open-pe/smart-shunt-fw/doc/thermal emf.md

i did some measurements to show the effects of thermoelectric force.

ADC: INA228, 40mV range
Resistor: Riedon RSN 50A 50mV (1mΩ)
Connection: blank copper wire soldered on SMD pads, blank copper wire on shunt resistor (see pictures below)




C
