open-pe/smart-shunt-fw/doc/ads131.md

internal Vref=1.2V

to measure DC voltage over FSR, connect AIN- to Vref.
Then AIN+ can have a voltage of 2.4V relative to GND.
Voltage divider: 3/100kΩ
=> measure voltages up to 82.4 V

Resistors:

TNPU06033K01BZEN00 (3.01k, 5ppm/K)
TNPU0603100KBZEN00 (100k, 5ppm/K)

2ppm/K:
susumu RG2012L-333-L-T05 (33k)
vishay P2TC0603D1003LNTA (100k)

0.2ppm/K:
Y201575K0000T9L (75k)
Y1633125K000T9R (125k, 2512)
Y4027125K000T9R (125k, 2512)
Y1627100K000T9R (100k, 2512)
Y1628150K000T9R (150k, 2512)
Y162750K0000T9R (50k, 2512)
