open-pe/smart-shunt-fw/doc/chopper.md

# voltage
- some DMM (the DMM6500) have the ability to measure voltage ratio
- multiplexers
  - TMUX8612RUMR: 100V multiplexer (20Ω)
  - TMUX8212RUMR (7Ω)
