open-pe/smart-shunt-fw/doc/Data Logging.md

https://github.com/PhilippCo/meas_rpi

https://github.com/PhilippCo/testgear

mreps github multistrumentalist

https://www.eevblog.com/forum/metrology/raspberry-pi23-logging-platform-for-voltnuts/
