open-pe/smart-shunt-fw/doc/Shunt Resistors.md

Considerations choosing the shunt / burden / current sense resistor:

* Current sense amplifier voltage range. INA228 has 2 ranges: ±163.84 mV and ±40.96 mV

## Riedon RSN series 0.1% ±15ppm/°C

* +-0.02% temp range (15-80°C)
* 50mV or 100mV output (for ina228 the 50mV is a good choice)
* RSN-20 (13.3A cont.), 2.5 or 5 mOhm
* RSN-50 (33.3 A cont.), 1 or 2 mOhm

## RESI RTC/RTB 0.1% ±20ppm/°C

* RTCS0100B050Z00 0.5mΩ ±0.1% ±20ppm/°C
* RTBS0200B075Z00 0.375mΩ ±0.1% ±20ppm/°C

## Riedon RS series 0.25%

## Murata DMS series 0.25% 15ppm (discontinued)

## CN XIQI DC Shunt Resistor 0.5%
* datasheet: "The ambient temperature changes by 10 °C, and the output signal of the shunt does not
  exceed 50% error of the accuracy"

* no info about temp coefficient

# Very low temp coefficient

* VPG Foil Resistors
    * PSBWR0010B
    * PSBXR0050B 5mOhm 0.1% ±5ppm/°C

# Smart Current Sensor

* SSA-100 (0.1%)
* +- 0.1 % upper temp range (10-50°C)
* CMRR: -100dB @ DC
* SNR: VIN = 100 mVPP, fIN = 1 kHz, BW = 10 kHz 80dB min 84dB typica

# Calibration 
https://www.fluke.com/de-de/produkt/kalibratoren/elektrische-kalibrierung/elektrische-normale/a40b
https://www.goldeno.com/pictures/CH48T4HK.pdf

https://www.distrelec.de/en/power-resistor-100mohm-250w-isabellenhuette-rug-r100-tk1/p/16057585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
https://www.distrelec.de/en/power-resistor-10mohm-250w-isabellenhuette-rug-r010-tk1/p/16057583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
