open-pe/smart-shunt-fw/src/relay_mux.h

#pragma once

#include <Arduino.h>
#include <atomic>
#include "util.h"

/*
 * Coto 3502 relay mux, revision A -- two-channel differential input selector.
 *
 * Board: ~/dev/ee/hw/dmm-mux-TMUX862/relay-mux (DESIGN.md dated 2026-08-21) is the
 * authority for everything asserted here. Two Coto 3502-05-511 DPST Form-A reed
 * relays select input A or input B onto one isolated output pair; on this bench the
 * output goes through the ads1262-divider board into one ADS1262 input pair.
 *
 * WHAT THE HARDWARE DOES FOR US, and therefore what this driver must not duplicate:
 *
 *   NREQ_A  = not REQ_A
 *   NREQ_B  = not REQ_B
 *   VALID_A = ARM and REQ_A and NREQ_B
 *   VALID_B = ARM and REQ_B and NREQ_A
 *
 * One-hot is decoded in 74HCT11/74HCT14 logic, so "both requests high" energises
 * NEITHER coil: no firmware bug can COMMAND two coils at once. That is a statement
 * about coil drive and nothing more -- it does not prove the mechanical contacts
 * cannot overlap, which depends on release and operate times DESIGN.md still lists
 * as qualification items. A TPS3840 supervisor and a common-return MOSFET (Q3,
 * gated by ARM) cut coil current independently of either driver. Every J4 logic
 * input carries a 10k series resistor into a 100k pull-down, so all three lines LOW
 * -- which is also what a floating, unprogrammed or reset MCU presents -- means both
 * coils released.
 *
 * So there is no state to restore at boot, and a RESET releases both coils. A HANG
 * does not: a wedged task leaves the output latches driving whatever they last
 * drove, ARM included. DESIGN.md accepts static ARM for revision A and leaves a
 * watchdog-qualified ARM as an open system-level option; this firmware does not
 * provide one.
 *
 * WHAT THE HARDWARE DOES NOT DO, and is therefore this driver's whole job: the
 * documented switching sequence, and the waiting.
 *
 *   1. Deassert ARM.
 *   2. Set REQ_A = REQ_B = 0.
 *   3. Wait for contact release and dead time.
 *   4. Preload exactly one request.
 *   5. Assert ARM.
 *   6. Wait for relay AND measurement settling before accepting data.
 *
 * Steps 3 and 6 are the ones that cost real time, and skipping them does not fail
 * loudly -- it publishes a plausible voltage measured through a contact that was
 * still bouncing, or through the wrong input entirely.
 *
 * 3.3 V DRIVE: ARGUED, NOT GUARANTEED. J4's contract is that it receives at least
 * VOH 3.10 V. The logic inputs are ~110k to ground and draw ~30 uA, so an ESP32 pin
 * loaded this lightly sits at essentially VDD; 3.3 V through the 10k/100k divider
 * puts 3.0 V on the HCT input against a 2.0 V VIH, and 3.0 V on Q3's gate against
 * the PMV20XNEAR's 2.5 V specification. The arithmetic holds, but "VDD at 30 uA" is
 * a nominal-plus-light-load argument, not a datasheet VOH bound over supply,
 * temperature and cable drop -- and DESIGN.md leaves confirmation of all three
 * outputs open. MEASURE ARM/REQ_A/REQ_B at J4 before trusting a marginal harness.
 * The board still needs its own +5V_CTRL -- this drives logic only, never a coil.
 */
class RelayMux2 {
public:
    enum class Target : uint8_t { NONE = 0, CH_A = 1, CH_B = 2 };

    static const char *targetName(Target t) {
        switch (t) {
            case Target::CH_A: return "A";
            case Target::CH_B: return "B";
            default:           return "off";
        }
    }

    /* TIMING -- DELIBERATELY CONSERVATIVE, AND NOT YET QUALIFIED.
     *
     * DESIGN.md derives exactly one number for the delay-on network, 15.95 ms, and
     * it is the FASTEST corner (R = 0.80 M, C = 94.7 nF, VT+ = 1.2 V min). That
     * number exists to prove non-overlap -- it bounds how soon a coil can possibly
     * engage -- and it is the wrong end of the distribution for deciding when the
     * contact is definitely closed. The slow corner is not derived anywhere, and
     * DESIGN.md's open gates still say "Revision-A qualification must measure
     * contact release time" and "Logic timing and coil voltage do not prove contact
     * non-overlap". So these are engineering margins over an unmeasured quantity,
     * not datasheet limits.
     *
     * Nominal turn-on is around 1 M * 100 nF * ln(5/(5-VT+)) ~ 40 ms, and a slow
     * corner (R +20%, VT+ at the HCT14 maximum) lands near 65 ms. 250 ms is roughly
     * 4x that, plus reed operate time (sub-millisecond on the 3500 series), plus
     * bounce, plus the divider's own RC into the ADC.
     *
     * The cost of being generous is only rate: a full A/B alternation is about
     * 2 * (DEAD_TIME + SETTLE) plus the discarded conversions, so ~1 s. This is a
     * precision DC ratio front end, not a telemetry channel -- an averaging window
     * spans many alternations either way. TIGHTEN THESE ONLY AGAINST A SCOPE
     * TRACE of the actual contacts, which is what the board's qualification plan
     * asks for anyway; the console command below exists to make that measurement
     * possible without a rebuild. */
    /* DEAD TIME -- STILL A MARGIN OVER AN UNMEASURED QUANTITY (2026-09-03).
     *
     * Coto's 3500-series datasheet gives the 3502 a RELEASE TIME of 0.1 ms typical
     * (operate, including bounce, 0.75 ms). DO NOT SIZE THIS FROM THAT NUMBER --
     * an earlier revision of this comment did, and called 5 ms "50x the datasheet
     * release", which is not what the datasheet says about THIS board:
     *
     *   - The 0.1 ms is measured "At Nominal Coil Voltage, 30 Hz Square Wave" and
     *     the datasheet specifies no coil suppression at all. This board fits D3/D4,
     *     plain 1N4148W flyback diodes across the coils, which hold the coil current
     *     circulating with ~0.7 V of forcing and stretch the flux decay. DESIGN.md
     *     anticipates it in as many words: "change to a diode/Zener clamp only if
     *     the plain diode cannot meet dead-time requirements." The release time as
     *     built is an unmeasured MULTIPLE of 0.1 ms.
     *   - 0.1 ms is TYPICAL. Coto publishes no maximum.
     *
     * So DESIGN.md's open gate -- a scope-measured contact release time -- is not
     * closed, and this number is exactly what it was before the datasheet was read:
     * a margin.
     *
     * What makes 5 ms comfortable rather than brave is that the dead window is NOT
     * the primary non-overlap margin. On an A<->B alternation the INCOMING channel's
     * delay-on capacitor has been discharged for a whole dwell, so after ARM rises
     * that coil still needs 15.95 ms in its FASTEST corner (DESIGN.md, derived
     * expressly to bound how soon a coil can engage) before it can pull in. The dead
     * window is a SECOND, INDEPENDENT margin -- the one that survives a failed
     * delay-on network -- and 5 ms of it costs nothing at the current rate.
     *
     * NOTE FOR ANYONE TIGHTENING THIS FURTHER: the ADC cannot check your work.
     * A brief overlap dumps charge onto the divider output, which decays through
     * the divider's ~19.6 kOhm into 100 nF -- tau ~ 2 ms -- while the published
     * conversion ends 157 ms after ARM, some 80 tau later. A dead-time sweep read
     * by this ADC therefore returns "not detectable", never "not present". Use a
     * scope on the contacts, which is what DESIGN.md asked for in the first place. */
    static constexpr uint32_t DEAD_TIME_MS = 5;           ///< step 3: both coils released
    /// Lower clamp on the runtime dead time. Not a measurement -- see setDeadMs().
    static constexpr uint32_t DEAD_MIN_MS = 1;
    /* SETTLE -- 250 ms until 2026-09-03, when the reason for it was removed.
     *
     * 250 ms was a margin against the settling tail measured on this fixture, and
     * that tail was dielectric absorption in the shunt-adc board's X7R input caps.
     * With those replaced by C0G the tail is gone: the bias-vs-step slope at the
     * earliest reachable sample instant fell from -25.73 +- 0.86 to -0.24 +- 2.04
     * uV/V, consistent with zero (pwr-metering hw/shunt-adc finding F23).
     *
     * 30 ms is not an accuracy choice -- the published conversion still ends
     * 157 ms after ARM either way, because the converter free-runs and
     * DISCARD_SCANS = 2 lands the sample on the same conversion for ANY settle up
     * to one conversion period. It is a RATE choice: dead + settle <= 52.22 ms
     * keeps the dwell one whole conversion shorter. See the static_assert in
     * relay_mux_adc.h, which fails the build if that stops holding.
     *
     * IT WAS 45 ms FOR ONE DAY, AND THAT WAS TOO CLOSE TO THE EDGE. dead + settle
     * = 50 ms left 2.2 ms of margin against the 52.22 ms conversion, and the bench
     * spent most of its time on the wrong side of the boundary: round trips
     * quantised to 45 / 46 / 47 conversions (2.350 / 2.402 / 2.461 s) with 47 the
     * mode, against the 44 predicted. Cutting 15 ms moved the WHOLE distribution
     * down by one conversion per dwell, to 44 / 45 -- which a 15 ms change cannot
     * do to a ceil() of a 35-50 ms argument unless the argument is bigger than
     * dead + settle. It is: this timer is evaluated by realTimeTask, which also
     * ticks the mux and updates every sampler on each pass, so what gets rounded
     * up is dead + settle + LATENCY.
     *
     * 30 ms leaves 17.2 ms for that latency and stays 10 ms above SETTLE_FLOOR_MS.
     * Do not spend the margin. It does NOT buy determinism -- two thirds of round
     * trips still take the extra conversion, and that residual is unexplained (see
     * doc/relay-mux-front-end.md) -- but it is worth a whole conversion per dwell.
     *
     * The contact's own close is covered by the discards, not by this number: the
     * delay-on slow corner is 65 ms and the published conversion does not START
     * until 104.4 ms after ARM. */
    static constexpr uint32_t SETTLE_MS_DEFAULT = 30;    ///< step 6: contact closed and quiet

    /* Hard floor. No evidence from the ADC, however convincing, may publish a
     * sample sooner than this after ARM rises, because DESIGN.md's FASTEST
     * delay-on corner is 15.95 ms -- the contact CANNOT have closed before then.
     *
     * (An earlier comment said anything read before this is "the previous channel
     * holding still". That was wrong: steps 1-3 release BOTH coils during
     * DEAD_TIME_MS before ARM rises, so between ARM and contact close the ADC sees
     * an OPEN input, not the previous selection. The floor is still conservative,
     * but the misreading matters -- it is the same one that let the step guard in
     * relay_mux_adc.h treat "moved away from the other channel" as proof that this
     * channel had closed.)
     *
     * This is the one number in the settle path that is a real bound rather than
     * an estimate, and it is why the adaptive path cannot talk itself to zero. */
    static constexpr uint32_t SETTLE_FLOOR_MS = 20;

    /* Upper clamp on the runtime settle. Bounds both the auto-widen ratchet and a
     * fat-fingered console value; a settle beyond this is not a slow relay, it is
     * a fault worth reporting as one. */
    static constexpr uint32_t SETTLE_MAX_MS = 2000;

private:
    const uint8_t pinArm, pinReqA, pinReqB;

    enum class State : uint8_t {
        OFF,        ///< disarmed, no request, not switching
        DEAD_TIME,  ///< both requests cleared, waiting out contact release
        SETTLING,   ///< one request preloaded and ARM asserted, waiting for close
        SETTLED,    ///< contact believed closed and quiet; data may be trusted
    };

    State state = State::OFF;
    Target current = Target::NONE;   ///< what is (being) selected
    Target pending = Target::NONE;   ///< what select() asked for
    uint32_t tStateMs = 0;
    uint32_t tArmMs = 0;             ///< when ARM last rose; survives the SETTLED transition
    uint32_t armGen_ = 0;            ///< bumped once per ARM assertion (one per switch)
    uint32_t settleMs_ = SETTLE_MS_DEFAULT;
    uint32_t deadMs_ = DEAD_TIME_MS;
    uint32_t generation_ = 0;        ///< bumped once per entry into SETTLED
    bool begun = false;

    /// Written by any task via requestFromOtherTask(), consumed only in tick().
    std::atomic<uint8_t> inboxTarget{(uint8_t) Target::NONE};
    std::atomic<bool> inboxPending{false};

    void driveAll(bool arm, bool reqA, bool reqB) const {
        digitalWrite(pinArm, arm);
        digitalWrite(pinReqA, reqA);
        digitalWrite(pinReqB, reqB);
    }

public:
    RelayMux2(uint8_t pinArm, uint8_t pinReqA, uint8_t pinReqB)
        : pinArm(pinArm), pinReqA(pinReqA), pinReqB(pinReqB) {}

    /// False if any control pin is unassigned. 255 is settings.h's "not wired on
    /// this board" sentinel and pinMode(255) is an "Invalid IO" HAL error, not a
    /// no-op -- the same mistake that put three of them in every boot log when the
    /// INA228 mux backend was left enabled on a board with no mux.
    bool pinsConfigured() const {
        return pinArm != 255 && pinReqA != 255 && pinReqB != 255;
    }

    bool begin() {
        /* Idempotent. begin() is now called from setup() so the state machine runs
         * whether or not anything else on the board came up, and the ADC backend
         * calls it too; a second call must not reset a mux that is mid-sequence or
         * already settled on a channel. */
        if (begun) return true;
        if (!pinsConfigured()) {
            ESP_LOGE("relaymux", "control pins unset (ARM=%u REQ_A=%u REQ_B=%u); not starting",
                     pinArm, pinReqA, pinReqB);
            return false;
        }
        /* Level BEFORE direction. An output pin adopts its level at the moment it
         * becomes an output, so pinMode-then-write briefly drives whatever was in
         * the output latch -- and a stray high on ARM with a stale request latched
         * is a coil pulse. Writing first makes the first driven level a known LOW.
         * The board's own pull-downs cover the window before this runs. */
        digitalWrite(pinArm, LOW);
        digitalWrite(pinReqA, LOW);
        digitalWrite(pinReqB, LOW);
        pinMode(pinArm, OUTPUT);
        pinMode(pinReqA, OUTPUT);
        pinMode(pinReqB, OUTPUT);
        driveAll(LOW, LOW, LOW);
        state = State::OFF;
        current = Target::NONE;
        pending = Target::NONE;
        tStateMs = millis();
        begun = true;
        ESP_LOGI("relaymux", "ready: ARM=%u REQ_A=%u REQ_B=%u, dead %lums settle %lums",
                 pinArm, pinReqA, pinReqB,
                 (unsigned long) DEAD_TIME_MS, (unsigned long) settleMs_);
        return true;
    }

    /* CROSS-TASK COMMAND INBOX.
     *
     * select() mutates the state machine and MUST run only on the task that calls
     * tick() -- realTimeTask here. The console runs on appTask
     * (handleConsoleInput() is called from Telemetry::update()), so a console
     * command calling select() directly races tick().
     *
     * The race is not theoretical and not benign. select() writes `state` and
     * `tStateMs` as two separate stores; with `state` written first, tick() on the
     * other core can observe state == DEAD_TIME carrying the PREVIOUS tStateMs,
     * find the dead time already long expired, and assert ARM immediately. That
     * skips the entire contact-release wait -- the one thing this driver exists to
     * guarantee -- and re-energises the other coil while the first contact may
     * still be closed, briefly bridging two floating 0-80 V inputs.
     *
     * The board survives it: the 1 M/100 nF delay-on network cannot engage a coil
     * for at least ~16 ms (DESIGN.md's fastest corner), which is exactly why that
     * network exists. But that makes the hardware interlock load bearing in normal
     * operation instead of the backstop it is meant to be, which is precisely what
     * the comment in select() claims this driver does not do.
     *
     * So off-task callers post here and the RT task applies it in tick(), and the
     * state machine stays single-threaded by construction. A second request
     * arriving before the first is consumed replaces it -- last writer wins, which
     * is the right semantic for "what channel do you want" and cannot queue up
     * stale switching.
     *
     * std::atomic with explicit ordering, NOT volatile. volatile orders volatile
     * accesses against each other within one thread and nothing else: it is not a
     * synchronisation primitive and carries no release/acquire edge, so the
     * consumer has no guarantee of seeing the target store that preceded the flag
     * store. (An earlier version of this comment also claimed "one aligned 32-bit
     * store" -- both fields are a single byte, so that was wrong as well as
     * insufficient.) The release/acquire pair below is what actually publishes the
     * target, and the exchange makes claim-and-clear one operation. */
    void requestFromOtherTask(Target t) {
        inboxTarget.store((uint8_t) t, std::memory_order_relaxed);
        inboxPending.store(true, std::memory_order_release);   // publishes the store above
    }

    /// Drop an unconsumed request. Used when authority over the mux changes hands,
    /// where applying a request posted under the old owner would be wrong.
    void clearInbox() { inboxPending.store(false, std::memory_order_relaxed); }

    /// Ask for a channel. Idempotent: re-selecting what is already settled does
    /// NOT re-run the sequence, so a caller may spam this every pass without ever
    /// letting the contact stay closed long enough to measure through.
    ///
    /// NOT SAFE from a task other than the one calling tick() -- use
    /// requestFromOtherTask() for that.
    void select(Target t) {
        if (!begun) return;
        if (t == pending && (state != State::OFF || t == Target::NONE)) return;
        pending = t;
        /* Always enter through DEAD_TIME, including from OFF and including when
         * t == current. Steps 1-3 are unconditional in the documented sequence:
         * ARM drops and both requests clear before any new request is preloaded,
         * so no path exists where a request changes underneath an asserted ARM.
         * The hardware would decode that as "neither", but relying on the
         * interlock to cover a sequence violation means the interlock is load
         * bearing in normal operation instead of being the backstop it is. */
        driveAll(LOW, LOW, LOW);
        current = Target::NONE;
        /* Timestamp BEFORE the state it belongs to, always. Even now that the
         * cross-task path is gone this is the correct order: a state observed with
         * a stale timestamp expires instantly, and every failure of that kind
         * shortens a wait that exists for physical reasons. */
        tStateMs = millis();
        state = State::DEAD_TIME;
    }

    /// Release both coils and stop. The board reaches the same state on its own if
    /// this firmware dies; calling it explicitly just makes an intentional stop
    /// indistinguishable from one in the log.
    void off() { select(Target::NONE); }

    /// Non-blocking. Safe to call at any rate; it only looks at the clock.
    void tick() {
        if (!begun) return;
        /* exchange, not load-then-store: claim-and-clear is one operation, so a
         * request posted concurrently either loses the race and is seen next tick
         * or wins and re-arms the flag. Acquire pairs with the release above. */
        if (inboxPending.exchange(false, std::memory_order_acquire)) {
            select((Target) inboxTarget.load(std::memory_order_relaxed));
        }
        const uint32_t now = millis();
        switch (state) {
            case State::OFF:
            case State::SETTLED:
                break;

            case State::DEAD_TIME:
                if ((uint32_t) (now - tStateMs) < deadMs_) break;
                if (pending == Target::NONE) {
                    tStateMs = now;
                    state = State::OFF;
                    break;
                }
                // Steps 4 and 5: preload exactly one request, then arm.
                driveAll(LOW, pending == Target::CH_A, pending == Target::CH_B);
                driveAll(HIGH, pending == Target::CH_A, pending == Target::CH_B);
                current = pending;
                tStateMs = now;
                /* Separate from tStateMs, which the SETTLED transition overwrites.
                 * Everything measuring "how long did this contact take" needs an
                 * origin that survives the whole switch, and ARM rising is the
                 * only defensible one -- it is the instant the coil can first be
                 * energised. */
                tArmMs = now;
                ++armGen_;
                state = State::SETTLING;
                break;

            case State::SETTLING:
                if ((uint32_t) (now - tStateMs) < settleMs_) break;
                tStateMs = now;
                state = State::SETTLED;
                ++generation_;
                break;
        }
    }

    bool isSettled() const { return state == State::SETTLED; }

    /// True while both coils are released and neither contact should be closed.
    /// Exposed so a characterisation build can look at what the ADC reads in that
    /// window, which is the only direct evidence that the previous contact
    /// actually opened before the next one was armed.
    bool inDeadTime() const { return state == State::DEAD_TIME; }

    uint32_t deadMs() const { return deadMs_; }

    /* THE DEAD TIME IS A SAFETY INTERLOCK, NOT A SETTLING ALLOWANCE. It is what
     * keeps the two inputs from ever being connected to each other: shorten it
     * below the previous reed's release time and ARM rises while that contact is
     * still closed, tying A to B through the mux. With one input open that is
     * harmless; with two live sources it is a short between them.
     *
     * So this setter exists for characterisation, and a value derived on a rig
     * with an open input MUST NOT be adopted for one where both inputs are driven.
     * There is no clamp that can make a short dead time safe, so the floor here is
     * only a sanity bound. */
    uint32_t setDeadMs(uint32_t ms) {
        if (ms < DEAD_MIN_MS) ms = DEAD_MIN_MS;
        deadMs_ = ms;
        return deadMs_;
    }

    /// The channel whose contact is believed closed and quiet, or NONE. Callers
    /// must gate every published sample on this rather than on select()'s
    /// argument: the two differ for DEAD_TIME_MS + SETTLE_MS after every switch,
    /// which is exactly the window in which the data is wrong.
    Target settledTarget() const { return state == State::SETTLED ? current : Target::NONE; }

    Target requested() const { return pending; }

    /// Bumped once per arrival at SETTLED, so a consumer can tell "still the same
    /// closed contact" from "closed again since I last looked" without watching
    /// the state machine itself.
    uint32_t generation() const { return generation_; }

    /// Worst-case time from select() to trustworthy data, for callers sizing their
    /// own timeouts. Derived, never a second hardcoded copy. Uses the DEFAULT
    /// settle: this sizes compile-time constants, and a runtime-narrowed settle
    /// only ever makes the estimate more conservative.
    static constexpr uint32_t switchLatencyMs() { return DEAD_TIME_MS + SETTLE_MS_DEFAULT; }

    uint32_t settleMs() const { return settleMs_; }

    /// Milliseconds since ARM last rose. Meaningless before the first switch;
    /// callers gate on armGeneration() changing rather than on this value.
    uint32_t msSinceArm() const { return (uint32_t) (millis() - tArmMs); }

    /// Bumped once per ARM assertion, i.e. once per switch. A consumer watching
    /// the contact settle uses this to know a NEW switch began -- generation()
    /// only tells it one FINISHED, which is too late to have observed anything.
    uint32_t armGeneration() const { return armGen_; }

    /// Runtime settle override, for adopting a measured value without a reflash.
    /// Clamped to the hard floor; returns what actually took effect. NOT
    /// persisted -- a settle time is a claim about physics that should be
    /// re-established from data on each boot, not inherited from an NVS byte
    /// written by an experiment nobody remembers.
    uint32_t setSettleMs(uint32_t ms) {
        if (ms < SETTLE_FLOOR_MS) ms = SETTLE_FLOOR_MS;
        if (ms > SETTLE_MAX_MS) ms = SETTLE_MAX_MS;
        settleMs_ = ms;
        return settleMs_;
    }

    const char *stateName() const {
        switch (state) {
            case State::OFF:       return "off";
            case State::DEAD_TIME: return "dead-time";
            case State::SETTLING:  return "settling";
            case State::SETTLED:   return "settled";
        }
        return "?";
    }
};
