open-pe/smart-shunt-fw/src/adc/ina228.h

#pragma once

#ifdef TARGET_STM32H5
#include "esp_compat.h"
#else
#include <SPI.h>
#include <INA226_WE.h>
#endif

#include "i2c.h"

#include "settings.h"
#include "sampling.h"
#include "util.h"


class PowerSampler_INA228;

#ifndef IRAM_ATTR
#define IRAM_ATTR
#endif

void IRAM_ATTR ina228_alert0();

void IRAM_ATTR ina228_alert1();

void IRAM_ATTR ina228_alert2();

void IRAM_ATTR ina228_alert3();

/* Indexed by (i2c_addr - I2C_A0), so it must cover every ADD0 strap the part
 * offers: 0x40..0x43. It was sized 3 while only three ALERT pins existed, which
 * made a 0x43 device an out-of-bounds write at init() -- silently, since the
 * bounds are never checked here. */
PowerSampler_INA228 *ina228_instance[4] = {nullptr, nullptr, nullptr, nullptr};


//#define INA228_SLAVE_ADDRESS        0x40

#define INA228_CONFIG            0x00
#define INA228_ADC_CONFIG        0x01
#define INA228_SHUNT_CAL        0x02
#define INA228_SHUNT_TEMPCO        0x03
#define INA228_VSHUNT            0x04
#define INA228_VBUS            0x05
#define INA228_DIETEMP            0x06
#define INA228_CURRENT            0x07
#define INA228_POWER            0x08
#define INA228_ENERGY            0x09
#define INA228_CHARGE            0x0A
#define INA228_DIAG_ALRT        0x0B
#define INA228_SOVL            0x0C
#define INA228_SUVL            0x0D
#define INA228_BOVL            0x0E
#define INA228_BUVL            0x0F
#define INA228_TEMP_LIMIT        0x10
#define INA228_PWR_LIMIT        0x11
#define INA228_MANUFACTURER_ID    0x3E
#define INA228_DEVICE_ID        0x3F

#include<Wire.h>

// These two talk to the same bus as i2c.h, from the real-time task on the other core.
// A register read is a three-call sequence (write pointer, repeated start, read), so
// the whole sequence has to hold i2cLock -- not each call. See the comment in i2c.h.
bool readRegister(uint16_t addr, uint8_t reg, uint16_t *regValue) {
    I2cLock lock;
    if (!lock) return false;

    uint8_t MSByte = 0, LSByte = 0;
    bool success = true;
    Wire.beginTransmission(addr);
    success = Wire.write(reg) == 1;
    success &= Wire.endTransmission(false) == 0;
    success &= Wire.requestFrom(static_cast<uint8_t>(addr), static_cast<uint8_t>(2)) == 2;
    //i2cErrorCode = !success;
    if (Wire.available() == 2) {
        MSByte = Wire.read();
        LSByte = Wire.read();
        *regValue = (MSByte << 8) + LSByte;
        return true;
    } else {
        return false;
    }
}

bool readBuf(uint16_t addr, uint8_t reg, uint8_t *buffer, uint8_t len) {
    I2cLock lock;
    if (!lock) return false;

    bool success = true;
    Wire.beginTransmission(addr);
    success = Wire.write(reg) == 1;
    success &= Wire.endTransmission(false) == 0;
    success &= Wire.requestFrom(static_cast<uint8_t>(addr), len) == len;
    if (success && Wire.available() == len) {
        for (int i = 0; i < len; ++i)
            buffer[i] = Wire.read();
        return true;
        //return Wire.readBytes(buffer, len) == len;
        //MSByte = Wire.read();
        //LSByte = Wire.read();
        //LSByte = Wire.read();
        //*regValue = (MSByte<<8) + LSByte;
        return true;
    } else {
        return false;
    }
}

bool readBuf2(uint16_t addr, uint8_t reg1, uint8_t reg2, uint8_t *buffer, uint8_t len) {
    return false;
    // doesnt work like that:
    bool success = true;
    Wire.beginTransmission(addr);
    success = Wire.write(reg1) == 1;
    success &= Wire.write(reg2) == 1;
    success &= Wire.endTransmission(false) == 0;
    success &= Wire.requestFrom(static_cast<uint8_t>(addr), len) == len;
    if (success && Wire.available() == len) {
        for (int i = 0; i < len; ++i)
            buffer[i] = Wire.read();
        return true;
    } else {
        return false;
    }
}


class PowerSampler_INA228 : public PowerSampler {
    static constexpr auto I2C_A0 = 0x40;

    volatile bool new_data = false;

    //int readUICycle = 0;
    //bool readingU = false;

    Sample lastSample{};

    uint8_t i2c_port{0};

    TaskNotification notification;
    float current_LSB{};
    uint16_t adcConfig{0}; // last ADC_CONFIG written, replayed by startReading()

    // Diagnostic state for implausible VBUS readings. The INA228's analog VBUS range is
    // 0-85V; anything outside that is either ADC railing (code near 0x7FFFF from a real
    // transient exceeding full-scale) or I2C corruption (e.g., all-0xFF from a NAK, which
    // the sign extension turns into ~0V). These let us tell them apart from the serial log.
    float lastVoltage{NAN};
    uint32_t implausibleCount{0};
    int64_t lastImplausibleLog{0};
    uint32_t lastDiag{0}; // encoded: reason<<24 | sign<<20 | code&0xFFFFF; cleared by getSample()

    /**
     * when acFreq is != 0, it will sample current and voltage (no dietemp) at the lowest possible conversion time
     * and average samples over a full period. this rejects the ac signal, if it is periodic with the given frequency
     * the sample rate of the power sampler should be equal to this frequency. if its lower, sample acquisition is too slow
     * and you have to increase conversion time.
     * the ina229 with SPI should perform better
     */
    uint8_t acFreq = 0;
    uint8_t nplc = 1;
    uint16_t avgNum = 0, avgCnt = 0;

    struct {
        bool vbus: 1;
        bool shunt: 1;
    } channelState{
        .vbus = false,
        .shunt = true
    };

public:
    const uint8_t storageId;
    const uint8_t resistorSlot;
    const uint8_t i2c_addr;

    uint8_t getStorageId() const override { return storageId; };

    /* The derived slots (2 + idx for the U/I calibration, 8 + idx for
     * resistor/range) only stay collision-free for 0x40 and 0x41. A part at
     * 0x43 derives 5 and 11, which are TMP117 0x48 and mux channel B -- so an
     * INA228 above 0x41 must be given its slots explicitly. 255 keeps the
     * historical derivation for the addresses where it is correct. */
    explicit PowerSampler_INA228(uint8_t i2c_addr, uint8_t calibSlot = 255, uint8_t resistorSlot = 255)
        : storageId{(uint8_t) (calibSlot != 255 ? calibSlot : (2 + i2c_addr - I2C_A0))},
          resistorSlot{(uint8_t) (resistorSlot != 255 ? resistorSlot : (8 + i2c_addr - I2C_A0))},
          i2c_addr(i2c_addr) {
    }

    bool resetPeriphery() {
        // reset
        if (i2c_write_short(i2c_port, i2c_addr, INA228_CONFIG, 0x8000) != ESP_OK) {
            return false;
        }

        int inaAddrIdx = i2c_addr - I2C_A0;


        float resistor = 2e-3f, range = 38.0f; // default: vishay 2mOhm, .1%, 3W
        if (readCalibrationFactors(resistorSlot, resistor, range)) {
            ESP_LOGI("ina228", "Restore resistor/range settings: %.6f/%.6f", resistor, range);
        } else {
            ESP_LOGI("ina228", "Default resistor/range settings: %.6f/%.6f", resistor, range);
        }
        setResistorRange(resistor, range, false);


        std::array<uint8_t, 4> alertPins = {
            settings.Pin_INA22x_ALERT,
            settings.Pin_INA22x_ALERT2,
            settings.Pin_INA22x_ALERT3,
            settings.Pin_INA22x_ALERT4
        };
        std::array<void (*)(void), 4> alerts = {&ina228_alert0, &ina228_alert1, &ina228_alert2, &ina228_alert3};

        assert(inaAddrIdx >= 0 && inaAddrIdx < (int) alertPins.size());
        uint8_t readyPin = alertPins[inaAddrIdx];
        /* 255 = this strap has no ALERT line wired. Not fatal: hasData() re-reads
         * the register every 50 ms regardless of the interrupt ("maybe we missed
         * it?"), so an un-alerted part still samples at 20 Hz -- far above the
         * ~2.5 SPS on-air rate. It loses the low-latency path, not the data. */
        if (readyPin != 255) {
            pinMode(readyPin, INPUT_PULLUP);
            attachInterrupt(digitalPinToInterrupt(readyPin), alerts[inaAddrIdx], FALLING);
        } else {
            ESP_LOGI("ina228", "0x%02hhX: no ALERT pin configured, polling at 20 Hz", i2c_addr);
        }


        uint16_t adc_config = 0;

        // conversion times see https://www.ti.com/lit/ds/symlink/ina228.pdf#page=22
        constexpr auto CT_50u = 0x0, CCT_84u = 0x1, CCT_150u = 0x2, CT_280u = 0x3,
                CT_540u = 0x4, CT_1052u = 0x5, CT_4120u = 0x7;

        constexpr auto BitPos_MODE = 12;
        constexpr auto MODE_ContBusV = 0x9, MODE_ContShuntV = 0xA,
                MODE_ContBus_ShuntV = 0xB,
                MODE_ContBusV_Temp = 0xD,
                MODE_Cont_ShuntV_Temp = 0xE,
                MODE_Cont_BusV_ShuntV_Temp = 0xF;
        constexpr auto MODE_SingleShot_BusV = 0x1, MODE_SingleShot_BusV_Temp = 0x5;
        constexpr auto AVG_1 = 0x0, AVG_4 = 0x1, AVG_16 = 0x2;

        if (acFreq) {
            // AC: https://www.ti.com/lit/an/slaa638a/slaa638a.pdf#page=10
            adc_config |= MODE_ContBus_ShuntV << BitPos_MODE; // MODE   = Continuous shunt and bus voltage

            // 280us is the shortest conversion time with i2c bus @ 800 khz
            // 150us is almost doable, reaches sps=41.2 instead of 50
            // so with 280u we'll have some head-room
            adc_config |= CT_280u << 9; // VBUSCT  = bus voltage conversion time
            adc_config |= CT_280u << 6; // VSHCT   = shunt voltage conversion time
            const auto totalConvTime = 2 * 280e-6f;

            avgNum = (uint16_t) rintf((float) nplc / (acFreq * totalConvTime));
            avgCnt = 0;
            ESP_LOGI("ina228", "measuring ac with freq %hhu, nplc=%i, averaging %hu", acFreq, (int) nplc, avgNum);

            adc_config |= AVG_1 << 0;

            // sps = 1/(84us+84us) * avgNum
        } else {
            uint8_t mode;
            if (channelState.shunt && channelState.vbus) {
                mode = MODE_Cont_BusV_ShuntV_Temp;
                adc_config |= CT_1052u << 9; // VBUSCT  = bus voltage conversion time
                adc_config |= CT_4120u << 6; // VSHCT   = shunt voltage conversion time
            } else if (channelState.vbus) {
                mode = MODE_ContBusV_Temp;
                adc_config |= CT_4120u << 9; // VBUSCT
            } else if (channelState.shunt) {
                mode = MODE_Cont_ShuntV_Temp;
                adc_config |= CT_4120u << 6; // VSHCT
            } else {
                assert(false);
            }

            adc_config |= mode << BitPos_MODE;
            adc_config |= CCT_84u << 3; // temperature conversion time
            adc_config |= AVG_16 << 0;

            // total period : 8324us => 120 Hz
            // total period : 2*1052+84us => 457 Hz
        }

        // total 1/((1052-6+1052-6) * 1)

        adcConfig = adc_config;
        return writeAdcConfig();
    }

    /// The ADC_CONFIG + DIAG_ALRT writes on their own, so a stalled device can be
    /// re-armed without re-running discovery and calibration. Errors are reported,
    /// not fatal: these used to be ESP_ERROR_CHECK, i.e. one failed I2C write on a
    /// contended bus took the whole logger down with an abort().
    bool writeAdcConfig() {
        if (i2c_write_short(i2c_port, i2c_addr, INA228_ADC_CONFIG, adcConfig) != ESP_OK) {
            ESP_LOGE("ina228", "0x%02hhX: ADC_CONFIG write failed", i2c_addr);
            return false;
        }

        uint16_t diagAlrt = 0;
        diagAlrt |= 0x1 << 14; // CNVR: enable conversion ready flag on ALERT pin
        if (i2c_write_short(i2c_port, i2c_addr, INA228_DIAG_ALRT, diagAlrt) != ESP_OK) {
            ESP_LOGE("ina228", "0x%02hhX: DIAG_ALRT write failed", i2c_addr);
            return false;
        }
        return true;
    }


    /// True when `pin` is not claimed by the board pin map, i.e. driving it is safe.
    /// Deliberately conservative: anything settings_t names is off limits.
    static bool probePinIsFree(int pin) {
        const uint8_t claimed[] = {
            (uint8_t) settings.Pin_I2C_SDA, (uint8_t) settings.Pin_I2C_SCL,
            settings.Pin_INA22x_ALERT, settings.Pin_INA22x_ALERT2,
            settings.Pin_INA22x_ALERT3, settings.Pin_INA22x_ALERT4,
            settings.Pin_Mux_S1, settings.Pin_Mux_S2, settings.Pin_Mux_Zero,
        };
        for (uint8_t c: claimed)
            if (c != 255 && c == (uint8_t) pin) return false;
        return true;
    }

    bool pinsAreShorted(int a, int b) {
        pinMode(a, INPUT_PULLUP);
        pinMode(b, OUTPUT);
        digitalWrite(b, LOW);
        usleep(1);
        if (digitalRead(a)) return false;
        digitalWrite(b, HIGH);
        usleep(1);
        return digitalRead(a);
    }

    bool init() {
        if (ina228_instance[i2c_addr - I2C_A0]) {
            return false;
        }


        ESP_LOGI("ina228", "Manufacturer ID:    0x%04X",
                 i2c_read_short(i2c_port, i2c_addr, INA228_MANUFACTURER_ID));
        auto deviceId = i2c_read_short(i2c_port, i2c_addr, INA228_DEVICE_ID);
        ESP_LOGI("ina228", "Device ID:          0x%04X", deviceId);

        if (deviceId != 0x2280 && deviceId != 0x2281) {
            if (deviceId != 0)ESP_LOGW("ina228", "This is not an INA228 device!");
            return false;
        }

        //channelState.shunt
#ifndef TARGET_STM32H5
        /* Strap probe: a jumper between GPIO7 and GPIO8 on the sensor board means
         * "vbus only". It cannot run unconditionally, because it DRIVES GPIO8 and
         * leaves GPIO7 an input -- on the XIAO those two are Pin_Mux_S2 and
         * Pin_Mux_Zero, already owned by INA228MuxBackend (which inits first). The
         * probe then reads back the level it just drove and "detects" a short that
         * is not there, silently disabling the shunt channel of whichever INA228
         * initialises after the mux -- while also leaving the mux's select line
         * floating as an input. Seen on 2026-09-02, the moment a second INA228
         * (0x43) was registered on the XIAO: it came up vbus-only every boot.
         *
         * A pin the board map has already assigned is not a free strap, so skip. */
        if (probePinIsFree(7) && probePinIsFree(8)) {
            if (pinsAreShorted(7, 8)) {
                sleep(1);
                ESP_LOGI("ina228", "pins 7 & 8 are shorted, measuring vbus only");
                sleep(1);
                channelState.shunt = false;
                channelState.vbus = true;
            }
        } else {
            ESP_LOGI("ina228", "0x%02hhX: GPIO7/8 are assigned on this board, "
                               "skipping the vbus-only strap probe", i2c_addr);
        }
#endif



        if (!resetPeriphery()) {
            return false;
        }

        ina228_instance[i2c_addr - I2C_A0] = this;

        return true;
    }

    bool shuntLv = false;

    void setShuntLowVoltageRange(bool _40_96_mV) {
        uint16_t config = 0;
        auto adc_range = (_40_96_mV ? 0x1 : 0x0);
        config |= adc_range << 4; // ADC shunt voltage range: 0h = ±163.84 mV, 1h = ± 40.96 mV
        if (i2c_write_short(i2c_port, i2c_addr, INA228_CONFIG, config) != ESP_OK) {
            ESP_LOGE("ina228", "0x%02hhX: CONFIG write failed", i2c_addr);
        }
        shuntLv = _40_96_mV;
        ESP_LOGI("ina228", "Set shunt %s mV range", shuntLv ? "40.96" : "163.84");
    }


    void setResistorRange(float resistor, float range, bool store = true) {
        // https://www.ti.com/lit/ds/symlink/ina228.pdf#page=31

        float maxExpectedVoltage = resistor * range;

        assert(maxExpectedVoltage > 1e-3f);
        assert(maxExpectedVoltage < 163.84e-3f);

        setShuntLowVoltageRange((maxExpectedVoltage < 40.96e-3f));

        current_LSB = range / std::pow(2.f, 19.f);
        //auto lsbRound =  std::pow(2.f, std::ceil(std::log2(current_LSB))); // round
        //ESP_LOGI("ina228", "round current_LSB %.7f to %.7f", current_LSB, lsbRound);

        //current_LSB = (float) range / (float) (2 << (19 - 1));
        //currentDivider_mA = 0.001/current_LSB;
        // pwrMultiplier_mW = 1000.0*25.0*current_LSB;

        auto shuntCal = 13107.2e6f * current_LSB * resistor;
        if (shuntLv) // adc_range = 1
            shuntCal *= 4;
        // auto shuntCalShort = (uint16_t) std::lround(shuntCal);
        auto shuntCalShort = (uint16_t) std::lround(shuntCal);

        current_LSB = (float) shuntCalShort / 13107.2e6f / resistor;

        ESP_LOGI("ina228", "Set shuntCal %hu (from %f), Vmax_exp=%.1fmV, current_LSB=%.7f", shuntCalShort, shuntCal,
                 maxExpectedVoltage * 1e3f, current_LSB);

        if (i2c_write_short(i2c_port, i2c_addr, INA228_SHUNT_CAL, shuntCalShort) != ESP_OK) {
            ESP_LOGE("ina228", "0x%02hhX: SHUNT_CAL write failed", i2c_addr);
        }

        if (store)
            storeCalibrationFactors(resistorSlot, resistor, range);
    }

    void startReading() {
        // Called by EnergyCounter when this sampler has gone quiet. This used to be an
        // empty stub, so the stall path "retried" a dead INA228 by doing nothing at all
        // (and then blocking the real-time task for up to 10 s to celebrate). Rewriting
        // ADC_CONFIG and re-enabling the conversion-ready alert is the corrective action
        // that actually recovers the two failures seen here: a device that reset itself
        // back to defaults, and a lost CNVR alert configuration.
        if (adcConfig) writeAdcConfig();
    }

    void alertNewDataFromISR() {
        new_data = true;
        notification.notifyFromIsr();
    }

    bool inOverflow = false;

    unsigned long tLastDataCheck = 0;

    bool hasData() override {
        if (!new_data) {
            notification.subscribe();
            if (!notification.wait(1) || !new_data) {
                if (micros() - tLastDataCheck < 50000)
                    return false; // every 50ms read the register regardless if interrupt happened (maybe we missed it?)
            }
        }

        tLastDataCheck = micros();
        new_data = false;

        //auto diagAlrt = i2c_read_short(i2c_port, i2c_addr, INA228_DIAG_ALRT);

        // this is faster:
        uint16_t diagAlrt = 0;
        readRegister(i2c_addr, INA228_DIAG_ALRT, &diagAlrt);

        bool CNVRF = (diagAlrt >> 1) & 0x1;
        bool BUSOL = (diagAlrt >> 4) & 0x1;
        bool SHNTOL = (diagAlrt >> 6) & 0x1;
        bool MATHOF = (diagAlrt >> 9) & 0x1;

        if (BUSOL) {
            ESP_LOGW("ina228", "Bus-Voltage over-load!");
        }
        if (SHNTOL) {
            ESP_LOGW("ina228", "Shunt-Voltage over-load!");
        }
        if (MATHOF) {
            if (!inOverflow)
                ESP_LOGW("ina228", "Math over-flow!");
            inOverflow = true;
        } else if (inOverflow) {
            ESP_LOGW("ina228", "Math over-flow resolved!");
            inOverflow = false;
        }

        if (CNVRF) {
            if (acFreq) {
                // accumulate
                if (avgCnt == 0) lastSample.u = lastSample.i = 0.0f;
                //auto u = read_voltage();
                //auto i = read_current();
                float u, i;
                //read_voltage_current(u, i);
                u = read_voltage();
                bool measureCurrent = false;
                i = measureCurrent ? read_current() : NAN;
                lastSample.u += u;
                lastSample.i += i;
                lastSample.p_ += u * i;
                ++avgCnt;
                if (avgCnt % avgNum == 0) {
                    avgCnt = 0;
                    return true;
                }
            } else {
                return true;
            }
        }
        return false;
    }

    float read_voltage() {
        int32_t iBusVoltage;
        float fBusVoltage;
        bool sign;

        if (!readBuf(i2c_addr, INA228_VBUS, (uint8_t *) &iBusVoltage, 3)) {
            ESP_LOGE("i2c", "0x%02hhX: err reading voltage", i2c_addr);
            return NAN;
        }

        uint8_t rawBytes[3];
        memcpy(rawBytes, &iBusVoltage, 3);

        sign = iBusVoltage & 0x80;
        iBusVoltage = __bswap32(iBusVoltage & 0xFFFFFF) >> 12;
        uint32_t adcCode = (uint32_t)(iBusVoltage & 0xFFFFF);
        if (sign) iBusVoltage += 0xFFF00000;
        fBusVoltage = (iBusVoltage) * 0.0001953125;

        // Diagnostic: log implausible VBUS readings to distinguish analog railing from
        // I2C corruption. Rate-limited to 1/s to avoid flooding the serial console.
        // raw=[7F FF F0] code=0x7FFFF sign=0 -> ADC max positive code (real railing)
        // raw=[FF FF FF] code=0xFFFFF sign=1 -> I2C NAK (all-1s, sign-extended to ~0V)
        const char *reason = nullptr;
        uint8_t reasonCode = 0;
        if (fBusVoltage > 85.0f || fBusVoltage < -1.0f) {
            reason = "out-of-range";
            reasonCode = 1;
        } else if (!std::isnan(lastVoltage) && std::fabs(fBusVoltage - lastVoltage) > 10.0f) {
            reason = "jump";
            reasonCode = 2;
        }
        if (reason) {
            lastDiag = (reasonCode << 24) | ((uint32_t)sign << 20) | (adcCode & 0xFFFFF);
            int64_t now = esp_timer_get_time();
            if (now - lastImplausibleLog > 1000000) {
                lastImplausibleLog = now;
                ++implausibleCount;
                ESP_LOGW("ina228", "0x%02hhX VBUS %s: %.3fV (prev %.3fV) raw=[%02hhX %02hhX %02hhX] code=0x%05X sign=%d count=%lu",
                         i2c_addr, reason, fBusVoltage, lastVoltage,
                         rawBytes[0], rawBytes[1], rawBytes[2],
                         adcCode, (int)sign, implausibleCount);
            }
        }
        lastVoltage = fBusVoltage;

        return (fBusVoltage);
    }

    float read_current() {
        int32_t iCurrent;
        float fCurrent;
        bool sign;

        //i2c_read_buf(i2c_port, i2c_addr, INA228_CURRENT, (uint8_t *) &iCurrent, 3);
        // faster:
        if (!readBuf(i2c_addr, INA228_CURRENT, (uint8_t *) &iCurrent, 3)) {
            ESP_LOGE("i2c", "err reading current");
            return NAN;
        }

        sign = iCurrent & 0x80;
        iCurrent = __bswap32(iCurrent & 0xFFFFFF) >> 12;
        if (sign) iCurrent += 0xFFF00000;
        if (shuntLv) // adc_range = 1?
            iCurrent = iCurrent / 4;

        fCurrent = (float) (iCurrent) * current_LSB;

        return (fCurrent);
    }

    static inline int32_t readTwosComplement24(uint8_t *buf) {
        int32_t i = __bswap32(*(int32_t *) buf & 0xFFFFFF) >> 12;
        bool sign = buf[0] & 0x80;
        if (sign) i += 0xFFF00000;
        return i;
    }

    bool read_voltage_current(float &fBusVoltage, float &fCurrent) const {
        uint8_t buf[6];
        if (!readBuf2(i2c_addr, INA228_VBUS, INA228_CURRENT, buf, 6)) {
            ESP_LOGE("i2c", "err reading voltage and current");
            return false;
        }

        fBusVoltage = (float) readTwosComplement24(buf) * 0.0001953125f;

        auto iCurrent = readTwosComplement24(buf + 3);
        if (shuntLv) // adc_range = 1?
            iCurrent = iCurrent / 4;
        fCurrent = (float) (iCurrent) * current_LSB;

        return true;

        /*
                //i2c_read_buf(i2c_port, i2c_addr, INA228_VBUS, (uint8_t *) &iBusVoltage, 3);

                if(!readBuf(i2c_addr, INA228_VBUS,  (uint8_t *) &iBusVoltage, 3)) {
                    ESP_LOGE("i2c", "err reading voltage");
                    return NAN;
                }


                iBusVoltage = __bswap32(iBusVoltage & 0xFFFFFF) >> 12;
                if (sign) iBusVoltage += 0xFFF00000;
                fBusVoltage = (iBusVoltage) * 0.0001953125;

                return (fBusVoltage);




                //i2c_read_buf(i2c_port, i2c_addr, INA228_CURRENT, (uint8_t *) &iCurrent, 3);
                // faster:
                if(!readBuf(i2c_addr, INA228_CURRENT,  (uint8_t *) &iCurrent, 3)) {
                    ESP_LOGE("i2c", "err reading current");
                    return NAN;
                }



                return (fCurrent);
                */
    }

    float read_dietemp() {
        int16_t regVal;

        //i2c_read_buf(i2c_port, i2c_addr, INA228_DIETEMP, (uint8_t *) &regVal, 2);
        //regVal = __bswap16(regVal);

        if (!readRegister(i2c_addr, INA228_DIETEMP, (uint16_t *) &regVal)) {
            ESP_LOGE("i2c", "err reading dietemp");
            return NAN;
        }

        return regVal * 7.8125e-3f;
    }

    Sample getSample() {
        lastSample.setTimeNow();

        if (acFreq) {
            assert(avgCnt == 0);
            float n = 1.f / (float) avgNum;
            //avgCnt = 0;
            lastSample.u *= n;
            lastSample.i *= n;
            lastSample.p_ *= n;
        } else {
            lastSample.u = channelState.vbus ? read_voltage() : NAN;
            lastSample.i = channelState.shunt ? read_current() : NAN;
            lastSample.temp = read_dietemp();
        }

        lastSample.diag = lastDiag;
        lastDiag = 0;

        //float busP = ina226.getBusPower();
        //float pErr = std::abs(lastSample.p() - busP) / busP;
        //if (pErr > 0.001f) {
        //ESP_LOGW("ina226", "Bus power %.3fW deviates from computed %.3fW ", busP, lastSample.p());
        //}


        return lastSample;
    }
};

void IRAM_ATTR ina228_alert0() {
    if (ina228_instance[0])ina228_instance[0]->alertNewDataFromISR();
}

void IRAM_ATTR ina228_alert1() {
    if (ina228_instance[1])ina228_instance[1]->alertNewDataFromISR();
}

void IRAM_ATTR ina228_alert2() {
    if (ina228_instance[2])ina228_instance[2]->alertNewDataFromISR();
}

void IRAM_ATTR ina228_alert3() {
    if (ina228_instance[3])ina228_instance[3]->alertNewDataFromISR();
}
