open-pe/smart-shunt-fw/src/ble.h

#pragma once

/*
  Complete Getting Started Guide: https://RandomNerdTutorials.com/esp32-bluetooth-low-energy-ble-arduino-ide/
  Based on Neil Kolban example for IDF: https://github.com/nkolban/esp32-snippets/blob/master/cpp_utils/tests/BLE%20Tests/SampleServer.cpp
  Ported to Arduino ESP32 by Evandro Copercini


indicuations:
https://community.silabs.com/s/article/x-deprecated-kba-bt-0102-ble-basics-master-slave-gatt-client-server-data-rx-x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,therefore%20faster%2C%20but%20less%20reliable.
"It will be followed up by the gecko_evt_gatt_server_characteristic_status event with status_flags = 0x2 when the acknowledgement comes back from the GATT client."
NimBLECharacteristicCallbacks::onStatus
*/

//#define USE_ARDUINO_BLE 0

#ifdef USE_ARDUINO_BLE
#include <BLEDevice.h>
#include <BLEUtils.h>
#include <BLEServer.h>
#else
#include <Arduino.h>
#include <NimBLEDevice.h>
#include <NimBLELocalValueAttribute.h> // NIMBLE_PROPERTY
#endif

#include <esp_log.h>

#include <mutex>
#include <string>

#include <ota_ble.h>

#include "aux_switch.h"
#include <esp_system.h>
#include <soc/rtc_cntl_reg.h>

// See the following for generating UUIDs:
// https://www.uuidgenerator.net/

#define SERVICE_UUID        "e8308d3d-c3b4-45ff-ba58-9c0fb99d0ecb"
#define CHARACTERISTIC_UUID "df51a73d-0b60-43a5-bc86-a043f3841152"

// OTA firmware push, on the same service as the telemetry characteristic. Control and status share
// one characteristic (fugu splits them only because it is reusing a console); firmware bytes get
// their own write-no-response characteristic because that is the only high-throughput path.
#define OTA_CTRL_CHAR_UUID  "b0e0d1a4-7f52-4a3e-9c61-2d8f5b3ae741"
#define OTA_DATA_CHAR_UUID  "b0e0d1a5-7f52-4a3e-9c61-2d8f5b3ae741"

// Aux switch (see aux_switch.h). Value is a single ASCII '0'/'1' so a read or a notification is
// trivially parseable; writes additionally accept raw 0/1 and on/off/toggle.
#define AUX_CHAR_UUID       "b952dad5-9541-4852-bab6-96b9cbc9131a"

/// Set by the OTA quiesce hook, read by realTimeTask. Flash erase/write disables the CPU cache and
/// stalls the other core, so the sampling loop has to stand down for the duration of a transfer.
extern volatile bool g_samplingHalted;

#ifdef USE_ARDUINO_BLE
class BleSrv {
    BLECharacteristic *pCharacteristic = nullptr;

public:
    static constexpr uint16_t MTU = 256;
    static constexpr uint16_t MAX_PAYLOAD_LEN = MTU - 3;

    void begin() {
        BLEDevice::init("smart-shunt");
        BLEServer *pServer = BLEDevice::createServer();


        BLEService *pService = pServer->createService(SERVICE_UUID);
        pCharacteristic = pService->createCharacteristic(
            CHARACTERISTIC_UUID,
            BLECharacteristic::PROPERTY_READ |
            BLECharacteristic::PROPERTY_NOTIFY
        );

        pCharacteristic->setValue("\0\0\0\0");
        pService->start();
        // BLEAdvertising *pAdvertising = pServer->getAdvertising();  // this still is working for backward compatibility
        BLEAdvertising *pAdvertising = BLEDevice::getAdvertising();
        pAdvertising->addServiceUUID(SERVICE_UUID);
        pAdvertising->setScanResponse(true);
        //pAdvertising->setMinPreferred(0x06);  // functions that help with iPhone connections issue
        pAdvertising->setMinPreferred(0x12);
        // https://docs.espressif.com/projects/esp-idf/en/stable/esp32/api-reference/bluetooth/esp_gap_ble.html
        if (BLEDevice::setMTU(MTU) != ESP_OK) {
            ESP_LOGW("ble", "BLE server set MTU failed");
        }
        BLEDevice::startAdvertising();

        ESP_LOGI("ble", "BLE server started");
    }

    void setVal(const uint8_t *buf, size_t len) {
        if (pCharacteristic) {
            pCharacteristic->setValue(const_cast<uint8_t *>(buf), len);
            pCharacteristic->notify();
        }
    }
};
#else
#include "ble_transport.h"
class BleSrv : public BleTransport {
    BLEServer *pServer = nullptr;
    BLECharacteristic *pCharacteristic = nullptr;

public:
    static constexpr uint16_t MTU = 512; // lower than BLE_ATT_MTU_MAX
    static constexpr uint16_t MAX_PAYLOAD_LEN = MTU - 3;

    /// One telemetry record. bleBuf carries NOTHING ELSE: send() has exactly one
    /// caller, telemetry.h, which passes sizeof(WireSample); aux state and the
    /// OTA status stream use their own characteristics and never touch this
    /// buffer. So bleBufPos is always a whole multiple of this.
    ///
    /// Pinned by `if (sizeof(WireSample) != 64) assert(false)` in
    /// main_esp32.cpp/main_stm32.cpp -- ble.h does not include the telemetry
    /// headers, so the number is restated here rather than derived.
    static constexpr uint16_t RECORD_LEN = 64;

    /// Largest indication that is still a whole number of records: 448 for a
    /// 512-byte MTU, i.e. 7 records against the 509 bytes ATT would allow.
    ///
    /// RECORD ALIGNMENT IS THE POINT, and it is not cosmetic. flush() re-sends
    /// the same byte range when an ack does not arrive within ACK_TIMEOUT_MS,
    /// and if the peer DID receive that indication and merely acked late, those
    /// bytes enter the stream twice. The collector
    /// (pwr-metering/smart-shunt-ble-client.py) is a byte-stream reassembler --
    /// it splits on `len(d) % 64` and carries the remainder -- so duplicated
    /// bytes that are not a multiple of 64 shift every subsequent record
    /// boundary permanently, and _decode_frame()'s CRC assert then fires on
    /// every frame from then on.
    ///
    /// Clamping at 509 split records: 7 whole ones plus 61 bytes of the eighth.
    /// Clamping at 448 cannot, so a duplicated payload inserts WHOLE records.
    /// Those decode cleanly and are duplicates by idx, which is what flush()'s
    /// own comment already assumed the client would see -- that assumption was
    /// only true before the buffer grew past one payload, because bleBufPos was
    /// then always both the whole buffer and a multiple of 64.
    ///
    /// Costs nothing: 448 is exactly the payload the single-payload buffer used
    /// to ship, and the deep queue still drains across successive indications.
    static constexpr uint16_t MAX_INDICATE_LEN = (MAX_PAYLOAD_LEN / RECORD_LEN) * RECORD_LEN;
    static_assert(MAX_INDICATE_LEN >= RECORD_LEN,
                  "MTU too small to carry even one telemetry record");

    /// Queue depth, in whole records.
    ///
    /// Was MAX_PAYLOAD_LEN*1, i.e. exactly one payload (7 WireSamples). That gave
    /// the link no elasticity at all: one indication round trip measured ~600 ms
    /// on the bench, so any tick whose samples outran a single in-flight payload
    /// dropped the remainder -- 45 "buffer full" warnings in 50 s with a
    /// subscriber attached, and the dropped samples never reach InfluxDB, so the
    /// stored series is silently decimated rather than merely late.
    ///
    /// Then *4 (31 records, ~5 s of production at the bench's ~6 records/s).
    /// Still far too shallow for the stall that actually happens: the bench rpi
    /// shares one radio between three links, a continuous scan and a 20 s
    /// initiating window for a board that is switched off, and its own collector
    /// tears a link down after RX_TIMEOUT = 10 s of silence. A stall long enough
    /// to matter is by construction at least twice as long as 31 records buys.
    /// Measured on that board: the queue sat pinned at 1984/2036 bytes for tens
    /// of seconds, shedding ~3 samples/s the whole time.
    ///
    /// 256 records is ~42 s of production and 16 KB of BSS -- affordable on an
    /// ESP32-S3 and the difference between a stall costing LATENCY and a stall
    /// costing DATA. Sized in records, not payloads, because the queue's job is
    /// to hold samples over a stall: expressing it in payloads made the depth
    /// depend on MTU arithmetic that has nothing to do with how long a stall the
    /// bench needs to survive.
    ///
    /// (bleBufPos is a whole multiple of RECORD_LEN on every ordinary link, since
    /// send() appends whole records and flush() retires whole records -- but NOT
    /// on the degenerate sub-record-MTU path, where a partial ack leaves residue.
    /// Nothing here depends on the alignment; the drop-oldest path in send()
    /// checks it explicitly rather than assuming it.)
    static constexpr uint16_t QUEUE_RECORDS = 256;
    static constexpr auto bleBufLen = (uint16_t) (RECORD_LEN * QUEUE_RECORDS);
    uint8_t bleBuf[bleBufLen];
    uint16_t bleBufPos = 0;
    // How much of bleBuf the in-flight indication actually covers. send() keeps appending
    // while an indication is unacked, so the ack must only consume THIS many bytes -- an ack
    // that clears the whole buffer destroys every sample queued since the indication was cut
    // (that bug made the first energy counter's samples the only ones that ever arrived).
    //
    // Single-writer rule: the app task (send/flush) is the ONLY writer of bleBuf, bleBufPos,
    // inFlightLen and waitingForAck. The NimBLE host-task callbacks write nothing but the
    // single-byte flags below, which the next send()/flush() consumes -- so no lock is needed
    // across the two tasks.
    uint16_t inFlightLen = 0;
    // Whether the slow-link warning has already been issued for the CURRENT outstanding
    // indication. There is only ever one (see flush()), so this is a per-indication latch rather
    // than a rate limiter.
    bool ackWarned = false;
    volatile bool acked = false;      // onAck(done): the in-flight indication was confirmed
    volatile bool ackFailed = false;  // onAck(!done): it terminally failed; retire it unconsumed
    // The subscription changed (unsubscribe, resubscribe or disconnect). Consumed at the top of
    // send()/flush(), which discard the buffer: it belongs to the previous session. A flag (not
    // an app-task check of `subscribed`) because a quick unsub->resub or disconnect->reconnect
    // can complete WITHIN one 400ms send cadence, so the app task would never see the gap and
    // would ship the dead session's bytes to the new client.
    volatile bool sessionChanged = false;

    volatile bool subscribed = false; // whether the client subscribed for indications
    volatile uint8_t waitingForAck = 0; // in-transit; written by app task, read by onAck
    uint32_t tLastIndicate = 0;

    uint32_t nDroppedNoPeer = 0;   // discarded because nothing was subscribed
    uint32_t nDroppedBacklog = 0;  // discarded with a subscriber attached -- the real overflow
    // Overflow is a sustained condition, not an event: it used to log once per dropped sample,
    // ~3 lines/s forever, which drowned the sampler summaries in the very log you need to read to
    // diagnose it. Rate-limited to one line carrying the count since the last one, so the rate is
    // still visible without the volume.
    uint32_t tLastBacklogWarn = 0;
    uint32_t nDroppedSinceWarn = 0;
    static constexpr uint32_t WARN_INTERVAL_MS = 5000;

    // An indication that is never acknowledged must not park the buffer forever.
    //
    // NOW A DIAGNOSTIC THRESHOLD, NOT A RETRY TRIGGER -- see flush(), which waits an unacked
    // indication out instead of re-sending it. Crossing this logs "the link is slow"; it changes
    // no transfer state.
    //
    // The history is worth keeping, because it is what proved the retry was wrong. The value was
    // briefly cut from 5 s to 2 s, on the argument that the collector (pwr-metering) drops a link
    // silent for RX_TIMEOUT = 10 s, so two lost acks would cost the connection. Flashed at 2 s,
    // the board logged 309 failed indications in 7 minutes, every one NimBLE rc=6 = BLE_HS_ENOMEM
    // -- the retries were exhausting the proc/mbuf pools, i.e. the timeout was manufacturing the
    // congestion it was meant to survive.
    //
    // 5 s also brackets the real round trip usefully: at 2 s the threshold was crossed every
    // ~2.7 s, at 5 s roughly once per 25 s, so the congested bench adapter's true ack latency sits
    // between those figures. Below the worst LEGITIMATE round trip, this only cries wolf.
    static constexpr uint32_t ACK_TIMEOUT_MS = 5000;

    // The buffer must not park forever, and since flush() no longer re-sends, THIS is what
    // guarantees it. Above 30 s, NimBLE's own GATT timeout should already have terminated the
    // procedure and reported a failure status; if nothing has been reported by 35 s the ATT
    // bearer is stuck and, per spec, unusable for further transactions. Drop the link: the
    // session teardown discards the queue and the transfer state, and the collector reconnects
    // within seconds. Deliberately longer than NimBLE's timeout so the normal recovery -- a
    // reported failure, consumed by the ackFailed path -- always gets to happen first.
    static constexpr uint32_t ACK_STUCK_MS = 35000;

    // indicate() returning false means NimBLE could not take the payload right now. Measured on
    // the bench it is always rc=6, BLE_HS_ENOMEM: ble_gatts_indicate_custom() needs a
    // ble_gattc_proc AND an mbuf per call, and it never refuses on "one is already outstanding"
    // (see ACK_TIMEOUT_MS), so the only way it says no is by running out of one of those pools.
    // That makes it a BACKPRESSURE signal, not an error to retry through: the pools refill as the
    // queued ATT traffic drains. flush() now runs every app-task pass (~10 ms) rather than once
    // per 400 ms telemetry tick, so retrying blindly would hammer an already-empty pool 100x/s and
    // starve the OTA status notifies too. Back off for a connection interval instead.
    uint32_t tIndicateFailed = 0;
    uint32_t nIndicateFailed = 0;
    uint32_t nIndicateFailedSinceWarn = 0;
    uint32_t tLastIndicateWarn = 0;
    static constexpr uint32_t INDICATE_BACKOFF_MS = 100;

    // ---- OTA over BLE -------------------------------------------------------------------------
    BLECharacteristic *pOtaCtrl = nullptr;
    BLECharacteristic *pOtaData = nullptr;

    /// Negotiated ATT MTU. onMTUChange used to only print it; notifications have to be chunked to
    /// it, and CONFIG_BT_NIMBLE_ATT_PREFERRED_MTU=256 in the prebuilt libs caps the 512 we ask for,
    /// so the requested value is not the value we get.
    volatile uint16_t peerMtu = 23;
    volatile uint16_t connHandle = 0;
    volatile bool haveConn = false;

#ifdef BLE_STATUS_NEOPIXEL_PIN
    // Minimum nonzero WS2812 channel value: visible status with the least light.
    static constexpr uint8_t BLE_STATUS_BLUE_BRIGHTNESS = 1;
    /// -1 forces begin() to transmit black once; afterward the WS2812 only needs
    /// another frame when the displayed connection state changes.
    int8_t connectionLedState = -1;

    void updateConnectionLed(bool connected) {
        const int8_t next = connected ? 1 : 0;
        if (connectionLedState == next) return;
        rgbLedWrite(BLE_STATUS_NEOPIXEL_PIN, 0, 0,
                    connected ? BLE_STATUS_BLUE_BRIGHTNESS : 0);
        connectionLedState = next;
    }
#endif

    /// Pending connection-parameter change, applied from the app task. NOT from onConnect: issuing
    /// a device-initiated LL update synchronously inside the connect callback trips a controller
    /// assert (lld_con.c:3275) -- fugu paid for that one.
    enum class ConnParams : uint8_t { None, Default, Fast, LowPower };
    /// App task (tick()) is the ONLY writer -- see the single-writer rule above. There is
    /// deliberately no "wanted" companion field: nothing outside tick() gets to request a
    /// parameter change, because the steady-state answer is "ask for nothing".
    ConnParams connParamsApplied = ConnParams::None;

    /* Console-driven sweep override for the steady-state parameters. App task is still
     * the only thing that CALLS updateConnParams(); these are just the numbers it uses,
     * and requestConnParams() re-arms connParamsApplied so tick() reissues the request
     * on its next pass -- the console must never issue an LL update itself, for the
     * same controller-assert reason onConnect must not. */
    bool lowPowerOverride = false;
    uint16_t ovItvlMin = 80, ovItvlMax = 160, ovLatency = 3;

    /// OTA status stream (device -> host). The status hook appends here from the app task and the
    /// control characteristic's write callback appends from the NimBLE host task, so unlike the
    /// telemetry path this one genuinely needs a lock.
    std::string otaTx;
    std::mutex otaTxMutex;
    static constexpr size_t OTA_TX_CAP = 4096;
    uint32_t nOtaTxDropped = 0;

    inline static BleSrv *s_self = nullptr;

    // ---- aux switch --------------------------------------------------------------------------
    BLECharacteristic *pAuxChar = nullptr;
    /// Latched by the write callback on the NimBLE host task; applied by tick() on the app task,
    /// because setting the switch persists to NVS and that writes flash.
    volatile bool auxReqPending = false;
    /* Reboot-into-ROM-downloader request, latched by the OTA control characteristic.
     * BLE is the ONLY control channel that reaches the xiao_nest riser: its USB-CDC
     * is dead in BOTH directions (measured 2026-09-03 -- the console `download`
     * command was written to the port and never arrived, while the board carried on
     * streaming telemetry throughout), so without this every reflash costs a manual
     * BOOT+RESET at the bench. */
    volatile bool dlReqPending = false;
    volatile bool auxReqValue = false;
    /// Last value published to the characteristic, so tick() only notifies on an actual change.
    int8_t auxPublished = -1;

    void publishAux(bool on) override {
        if (!pAuxChar) return;
        const char v = on ? '1' : '0';
        pAuxChar->setValue((uint8_t *) &v, 1); // keep a plain read truthful, connected or not
        if (isConnected()) pAuxChar->notify((uint8_t *) &v, 1);
        auxPublished = on ? 1 : 0;
    }

    void otaStatusAppend(const char *line) {
        std::lock_guard<std::mutex> lk(otaTxMutex);
        if (otaTx.size() + strlen(line) + 1 > OTA_TX_CAP) {
            // Never silently: a dropped status line is a host that waits out a timeout instead of
            // learning what went wrong.
            ++nOtaTxDropped;
            ESP_LOGW("ble", "OTA status buffer full, dropped a line (%lu total)",
                     (unsigned long) nOtaTxDropped);
            return;
        }
        otaTx += line;
        otaTx += '\n';
    }

    static void otaStatusHook(OtaBleLevel level, const char *line) {
        // Mirrored to the UART log as well as the client -- during a bench OTA the serial console is
        // often the only view when the BLE link is the thing misbehaving.
        switch (level) {
            case OtaBleLevel::Info:  ESP_LOGI("otab", "%s", line); break;
            case OtaBleLevel::Warn:  ESP_LOGW("otab", "%s", line); break;
            case OtaBleLevel::Error: ESP_LOGE("otab", "%s", line); break;
        }
        if (s_self) s_self->otaStatusAppend(line);
    }

    static void otaQuiesceHook(bool halt) { g_samplingHalted = halt; }

    static void otaRestartHook() {
        Serial.flush();
        ESP.restart();
    }

    bool inTransmission() const { return waitingForAck > 0; }

    bool isConnected() const override { return pServer && pServer->getConnectedCount() > 0; }

    /// Sweep hook: set the steady-state connection parameters and make tick() reissue
    /// the request. Intervals are in 1.25 ms units, latency in events -- the LL's own
    /// units, so what is typed is what goes on the air.
    void requestConnParams(uint16_t itvlMin, uint16_t itvlMax, uint16_t latency) override {
        ovItvlMin = itvlMin;
        ovItvlMax = itvlMax;
        ovLatency = latency;
        lowPowerOverride = true;
        connParamsApplied = ConnParams::None; // force tick() to re-request
    }

    /// Negotiated link parameters, for the periodic status line. false when there is no
    /// link, so the caller prints "no link" rather than a stale set of numbers.
    /// intervalMs/timeoutMs are already converted out of the LL's 1.25 ms / 10 ms units.
    bool connSnapshot(float &intervalMs, uint16_t &latency, uint16_t &timeoutMs) const override {
        if (!pServer || !haveConn) return false;
        NimBLEConnInfo info = pServer->getPeerInfoByHandle(connHandle);
        const uint16_t itvl = info.getConnInterval();
        if (!itvl) return false; // handle went stale between haveConn and the lookup
        intervalMs = itvl * 1.25f;
        latency = info.getConnLatency();
        timeoutMs = info.getConnTimeout() * 10;
        return true;
    }

    BleSrv() : serverCallbacks{this}, chrCallbacks{this}, otaCtrlCallbacks{this}, auxCallbacks{this} {
    }

    void begin() override {
        assert(pServer == nullptr);
        BLEDevice::init("smart-shunt");

        /* TX power is deliberately NOT set here. It was, briefly, at -3 dBm; the sweep
         * that justified it then refuted it.
         *
         * Measured 2026-09-02, 240 s per point on the bench link: +9 dBm 64.50 C,
         * -3 dBm 64.62 C, -12 dBm 64.66 C. A 21 dB span moved the die 0.16 K, and not
         * even monotonically -- while a REPEAT of the -3 dBm point drifted 0.6 K from
         * its own first reading. The error bar is four times the effect. The reason is
         * structural, not a limit of the measurement: one indication per 400 ms, each a
         * fraction of a millisecond of transmit, against a CPU and a BLE controller
         * that never sleep (no CONFIG_BT_LE_SLEEP_ENABLE, no CONFIG_PM_ENABLE). Event
         * energy is a rounding error next to the always-on baseline.
         *
         * So reducing it spends link margin -- on a board with NO ANTENNA FITTED -- to
         * buy nothing measurable. Worse, it cannot even be checked: the collector
         * reports advertisement RSSI, and a connected peripheral does not advertise, so
         * the number is frozen for the life of the connection (see doc/power-thermal.md).
         * A knob whose benefit is unmeasurable and whose cost is unmeasurable defaults
         * to off.
         *
         * -D BLE_TX_POWER_DBM=<n> sets it explicitly, and the `bletx` console command
         * changes it at runtime, for whoever can measure RSSI properly. */
#ifdef BLE_TX_POWER_DBM
        if (!NimBLEDevice::setPower(BLE_TX_POWER_DBM)) {
            ESP_LOGW("ble", "setPower(%d dBm) failed, keeping stack default", BLE_TX_POWER_DBM);
        }
#endif

        if (!NimBLEDevice::setMTU(MTU)) {
            ESP_LOGW("ble", "BLE server set MTU failed");
        }
        pServer = BLEDevice::createServer();
        pServer->setCallbacks(&serverCallbacks);
        BLEService *pService = pServer->createService(SERVICE_UUID);
        pCharacteristic = pService->createCharacteristic(
            CHARACTERISTIC_UUID, NIMBLE_PROPERTY::READ | NIMBLE_PROPERTY::INDICATE);
        pCharacteristic->setCallbacks(&chrCallbacks);
        pCharacteristic->setValue("\0\0\0\0");

        pOtaCtrl = pService->createCharacteristic(
            OTA_CTRL_CHAR_UUID, NIMBLE_PROPERTY::WRITE | NIMBLE_PROPERTY::NOTIFY);
        pOtaCtrl->setCallbacks(&otaCtrlCallbacks);
        // Write-no-response only: an acked write per chunk would cap throughput at one packet per
        // connection interval, which is the difference between a one-minute push and a ten-minute one.
        pOtaData = pService->createCharacteristic(OTA_DATA_CHAR_UUID, NIMBLE_PROPERTY::WRITE_NR);
        pOtaData->setCallbacks(&otaDataCallbacks);

        pAuxChar = pService->createCharacteristic(
            AUX_CHAR_UUID, NIMBLE_PROPERTY::READ | NIMBLE_PROPERTY::WRITE | NIMBLE_PROPERTY::NOTIFY);
        pAuxChar->setCallbacks(&auxCallbacks);
        publishAux(auxGet()); // the pin already has its restored state; make a read reflect it

        pService->start();

        s_self = this;
        OtaBleHooks hooks;
        hooks.status = &BleSrv::otaStatusHook;
        hooks.quiesce = &BleSrv::otaQuiesceHook;
        hooks.restart = &BleSrv::otaRestartHook;
        otaBleInit(hooks);
        // BLEAdvertising *pAdvertising = pServer->getAdvertising();  // this still is working for backward compatibility
        BLEAdvertising *pAdvertising = BLEDevice::getAdvertising();
        pAdvertising->addServiceUUID(SERVICE_UUID);
        pAdvertising->enableScanResponse(true); //setScanResponse(true);
        //pAdvertising->setMinPreferred(0x06);  // functions that help with iPhone connections issue
        //pAdvertising->setMinPreferred(0x0C80);
        pAdvertising->setAdvertisingInterval(800); // 3200
        //pAdvertising->setM

        pAdvertising->start(); // BLEDevice::startAdvertising();
        // https://docs.espressif.com/projects/esp-idf/en/stable/esp32/api-reference/bluetooth/esp_gap_ble.html
        //BLEDevice::startAdvertising();
        ESP_LOGI("ble", "BLE server started");

#ifdef BLE_STATUS_NEOPIXEL_PIN
        updateConnectionLed(false);
#endif
    }

    /*
    void setVal(const uint8_t *buf, size_t len) {
        if (pCharacteristic) {
            //pCharacteristic->setValue(const_cast<uint8_t *>(buf), len);
            bool res = pCharacteristic->indicate(const_cast<uint8_t *>(buf), len);
            if (!res) {
                ESP_LOGW("ble", "BLE server indicate failed");
            }
        }
    }
    */

    /// App task only. Discard all transfer state; the buffer content died with its session.
    void consumeSessionChange() {
        if (!sessionChanged) return;
        sessionChanged = false;
        bleBufPos = 0;
        inFlightLen = 0;
        ackWarned = false;
        waitingForAck = 0;
        acked = false;
        ackFailed = false;
    }

    void send(const uint8_t *buf, size_t len) override {
        consumeSessionChange();
        if (otaBleActive()) {
            // Telemetry stands down for the duration of a firmware push: the sampler is halted
            // anyway, and indications would only compete with the OTA status notifies for the same
            // small mbuf pool. Dropped rather than queued: a firmware push takes minutes, so the
            // queue would overflow whatever its depth and the records would be stale on arrival.
            bleBufPos = 0;
            inFlightLen = 0;
            return;
        }
        if (!subscribed || !isConnected()) {
            // Nobody can receive this sample, so there is no point buffering it. The old
            // code queued it anyway: bleBuf filled up within a few seconds of running
            // unconnected and then EVERY subsequent sample logged "ble buf overflow",
            // once per sample, forever. That noise is not just untidy -- it is the same
            // message a genuine overflow *with a peer attached* produces, so the one
            // warning that matters was buried in thousands that did not.
            bleBufPos = 0;
            inFlightLen = 0;
            ++nDroppedNoPeer;
            return;
        }

        if (bleBufPos + len > bleBufLen) {
            // This one is real: a peer is subscribed and we still cannot keep up.
            //
            // DISCARD THE OLDEST QUEUED RECORD, NOT THIS ONE. Dropping the newest kept a full
            // queue full: every sample delivered was already the whole queue depth old, the
            // backlog never shrank, and the freshest measurement -- the one a live Grafana panel
            // is actually asking for -- was the one guaranteed to be thrown away. Dropping the
            // head instead bounds delivery latency at the queue depth and lets the queue walk
            // back down as soon as the link recovers. The same number of samples is lost either
            // way; this way they are the stale ones.
            //
            // The first inFlightLen bytes are off limits: an indication covering them is out on
            // the wire and the ack path consumes exactly that range from the front of bleBuf.
            // Shifting them would make the ack retire bytes it never carried. Only one indication
            // is ever outstanding (flush() no longer re-sends), so inFlightLen alone describes
            // the whole protected prefix.
            //
            // BOTH ENDS OF THE DELETED WINDOW MUST LAND ON A RECORD BOUNDARY, or this removes the
            // tail of one record and the head of the next and the collector decodes one spliced
            // frame from the halves that remain. Framing recovers -- exactly 64 bytes leave -- but
            // a corrupt record is worse than a missing one. Two ways the head can be misaligned,
            // both on the degenerate path where the negotiated MTU cannot carry even one record
            // and flush() deliberately ships unaligned bytes:
            //   - inFlightLen itself is mid-record (e.g. 20), so offset inFlightLen is not a
            //     boundary;
            //   - a PREVIOUS sub-record ack already consumed a non-multiple of 64 from the front,
            //     leaving bleBuf[0] mid-record even when inFlightLen is 0.
            // Only whole records are ever appended, so `bleBufPos % RECORD_LEN == 0` is exactly
            // the test for "the head is on a boundary" and catches the second case, which
            // checking inFlightLen alone does not. Fall back to dropping the newest, which leaves
            // the existing byte stream untouched.
            bool droppedOldest = false;
            if (inFlightLen % RECORD_LEN == 0 && bleBufPos % RECORD_LEN == 0
                && bleBufPos >= inFlightLen + len) {
                memmove(bleBuf + inFlightLen, bleBuf + inFlightLen + len,
                        bleBufPos - inFlightLen - len);
                bleBufPos -= len;
                memcpy(&bleBuf[bleBufPos], buf, len);
                bleBufPos += len;
                droppedOldest = true;
            }
            // else: the head is not droppable, so THIS sample is the loss. The warning says which,
            // because "dropping oldest" on a line where the newest was actually dropped would
            // misdescribe what happened to the data.
            ++nDroppedBacklog;
            ++nDroppedSinceWarn;
            const uint32_t now = millis();
            // `!tLastBacklogWarn ||` so the FIRST overflow always prints. Without it the zero
            // initialiser doubles as a 5 s post-boot mute, and a burst that starts and clears
            // inside that window is never reported at all. No interval is printed: ESP_LOGW
            // already stamps every line with millis(), so the rate is the difference between two
            // stamps -- and the one thing a computed interval could add here was a nonsense "in
            // the last 0ms" on the first line.
            if (!tLastBacklogWarn || now - tLastBacklogWarn >= WARN_INTERVAL_MS) {
                ESP_LOGW("ble", "buffer full with a subscriber attached, dropping %s sample "
                         "(%hu queued, %lu since the last warning, %lu total)",
                         droppedOldest ? "oldest" : "newest",
                         bleBufPos, (unsigned long) nDroppedSinceWarn,
                         (unsigned long) nDroppedBacklog);
                tLastBacklogWarn = now;
                nDroppedSinceWarn = 0;
            }
        } else {
            memcpy(&bleBuf[bleBufPos], buf, len);
            bleBufPos += len;
        }
        /* DELIBERATELY NO flush() HERE. Telemetry calls send() once per sampler
         * and then flush() once at the end of the tick (telemetry.h), so an
         * eager flush on the FIRST send shipped a single 64-byte sample and then
         * blocked every later send in that tick behind the in-flight ack --
         * visible in the log as a stream of "sending 64" against a 448-byte
         * capacity. At a ~600 ms round trip that caps throughput near 1.7
         * samples/s no matter how much buffer exists, which is what made a
         * 7-sample queue overflow.
         *
         * Letting the tick's own flush() send the accumulated batch puts up to
         * MAX_PAYLOAD_LEN into each round trip instead of one sample. Nothing
         * waits on an eager flush: Telemetry::update() runs flush() on every
         * app-task pass and again at the end of each 400 ms tick, so a partial
         * batch is never stranded. */
    }

    /// Drop every trace of the previous connection. Without this, a stale bleBufPos and a
    /// stale waitingForAck survive into the next connection, where they either ship a
    /// fragment of the old session or wedge flush() before it ever sends.
    void onDisconnected() {
        // Host-task context: flags only. The app task tears the transfer state down when it
        // consumes sessionChanged.
        subscribed = false;
        sessionChanged = true;
        /* Connection parameters do not survive the connection. Without this reset the
         * low-power request is made once in the process's life and every reconnection
         * afterwards silently runs on whatever the central chose -- which looks
         * identical in the log to a request that was made and honoured. */
        connParamsApplied = ConnParams::None;
        // Undelivered OTA status belongs to the session that just ended. Carrying it over would
        // hand the next client the previous one's READY/FAIL lines -- the same trap the telemetry
        // buffer avoids via sessionChanged, and it would desynchronise a host's line parser.
        {
            std::lock_guard<std::mutex> lk(otaTxMutex);
            otaTx.clear();
        }
    }

    /// App-task pump for everything that must not run on the NimBLE host task: the deferred
    /// connection-parameter change and the OTA status stream. Call once per app-task pass, after
    /// otaBleTick() so the lines it produced go out in the same pass.
    void tick() override {
        // Self-reconciling rather than hook-driven: an OTA wants a 7.5-15ms interval (the default
        // 30-60ms would stretch a 1.4MB image over minutes), and the link goes back to the relaxed
        // interval as soon as the transfer ends, however it ended.
        if (haveConn) {
            // Steady state: request NOTHING. Whatever the central negotiated is the central's
            // business, and here it is a deliberate choice -- the bench rpi widens its interval to
            // 100-200ms with a 4s supervision timeout because BLE and WiFi share one radio
            // (ble-conn-params.service). The old code overrode that with 30-60ms / 1.8s on every
            // connect, and the link died with an LL timeout (reason 546) roughly once a minute,
            // forever, which looked like flaky radio rather than the device arguing with its peer.
            //
            // The only time we ask for anything is during an OTA, where the transfer genuinely
            // needs the throughput -- and then we hand the link back when it is done.
            /* Steady state now ASKS, where it used to accept whatever the central chose.
             * What it asks for is slave latency: permission to skip connection events it
             * has nothing to say in. The interval is left where the bench central already
             * puts it (100-200 ms, ble-conn-params.service) -- that mitigation exists
             * because BLE and WiFi share one radio on the rpi, and fighting it is what
             * killed OTA transfers with an LL timeout twice.
             *
             * Latency is free for OUR traffic and costs only THEIRS. A peripheral with
             * data queued transmits at the next connection event no matter what latency
             * is set, so telemetry is not delayed by a single event; what is delayed is
             * central-to-device delivery -- an aux command, an OTA start -- by at most
             * latency * interval_max = 3 * 200 ms = 600 ms, inside the 1 s budget.
             *
             * Supervision timeout has to outlast the skipping or the link drops on a
             * quiet stretch: (1 + latency) * interval_max * 2 = 1.6 s against the 4 s
             * asked for here.
             *
             * OTA still takes the link back to latency 0 via Fast, because a transfer is
             * exactly the case where every central-to-device packet is on the hot path. */
            ConnParams want = otaBleActive() ? ConnParams::Fast : ConnParams::LowPower;
            if (want != connParamsApplied) {
                // 15-30ms during OTA, NOT the 7.5-15ms fugu uses. The bench rpi deliberately widens
                // its connection interval to 100-200ms (ble-conn-params.service) because BLE and
                // WiFi share one radio there, and asking for 7.5ms fought that mitigation: the link
                // died with an LL timeout after ~35s of transfer, reproducibly, twice. The pressure
                // for a tiny interval came from 20-byte writes anyway; with the MTU actually
                // negotiated (509-byte chunks) this is far more headroom than the transfer needs.
                if (want == ConnParams::Fast)
                    pServer->updateConnParams(connHandle, 12, 24, 0, 400);
                else if (want == ConnParams::LowPower && lowPowerOverride)
                    /* Sweep override, set from the console. Same code path as the
                     * default so an experiment cannot accidentally measure a
                     * different mechanism than the one that will ship. */
                    pServer->updateConnParams(connHandle, ovItvlMin, ovItvlMax, ovLatency, 400);
                else if (want == ConnParams::LowPower)
                    /* Same 100-200 ms window the central already asks for, plus 3 events
                     * of slave latency. A central is free to refuse or to shorten this;
                     * the periodic status line prints what was actually negotiated, so a
                     * refusal shows up as latency 0 rather than as a silent no-op. */
                    pServer->updateConnParams(connHandle, 80, 160, 3, 400);
                else
                    // Post-OTA: relax to the coex-friendly end, matching what the bench central
                    // asks for anyway. NOT the old 24/48/180, which is what caused the drops.
                    pServer->updateConnParams(connHandle, 80, 160, 0, 400);
                connParamsApplied = want;
            }
        }

        // Apply a latched aux request here rather than in the write callback: auxSet() persists to
        // NVS, and an NVS commit is a flash write -- the one thing the BLE host task must never do.
        if (dlReqPending) {
            dlReqPending = false;
            /* APP TASK, not the host callback that latched it: this never returns,
             * and killing the NimBLE host task from inside its own callback would
             * take the notification below with it. The delay is for the notify to
             * actually reach the air -- at a 100-200 ms connection interval one
             * interval is not enough, and the operator otherwise sees the link drop
             * with no confirmation of why. */
            ESP_LOGW("otab", "download-mode reboot requested over BLE");
            if (pOtaCtrl) {
                pOtaCtrl->setValue("OTAB DOWNLOAD");
                pOtaCtrl->notify();
            }
            delay(600);
            REG_SET_BIT(RTC_CNTL_OPTION1_REG, RTC_CNTL_FORCE_DOWNLOAD_BOOT);
            esp_restart();
        }
        if (auxReqPending) {
            auxReqPending = false;
            auxSet(auxReqValue);
        }
        // Aux state-change notification is handled centrally in Telemetry::update(),
        // which calls publishAux() for both BLE-originated and console-originated changes.
        // The one exception: on a reconnect (auxPublished == -1, set by onConnect), push
        // the current state so the new client sees it immediately.
        if (auxPublished == -1) {
            publishAux(auxGet());
        }

        drainOtaTx();

#ifdef BLE_STATUS_NEOPIXEL_PIN
        updateConnectionLed(haveConn);
#endif
    }

    /// Push queued OTA status bytes out with real backpressure. A failed notify means NimBLE's mbuf
    /// pool is empty; looping on it there exhausts the pool and silently drops packets, so we stop
    /// and pick up on the next tick when it has refilled.
    void drainOtaTx() {
        if (!pOtaCtrl || !isConnected()) return;
        const size_t chunk = peerMtu > 3 ? (size_t) (peerMtu - 3) : 20;
        for (;;) {
            std::string out;
            {
                std::lock_guard<std::mutex> lk(otaTxMutex);
                if (otaTx.empty()) return;
                size_t n = otaTx.size() < chunk ? otaTx.size() : chunk;
                out.assign(otaTx, 0, n);
                otaTx.erase(0, n);
            }
            if (!pOtaCtrl->notify((const uint8_t *) out.data(), out.size())) {
                // Put it back at the front; it never reached the peer.
                std::lock_guard<std::mutex> lk(otaTxMutex);
                otaTx.insert(0, out);
                return;
            }
        }
    }

    /// Emit the tail of a throttled warning burst. Without this the counters are only ever
    /// printed BY a later event of the same kind, so a burst that stops inside the throttle
    /// window is never reported at all -- and a burst that stops is exactly the one you would
    /// most like to see bounded ("47 dropped, then it recovered"). Called from flush(), which
    /// runs every app-task pass whether or not anything is going wrong.
    void drainWarnCounters() {
        const uint32_t now = millis();
        if (nDroppedSinceWarn && now - tLastBacklogWarn >= WARN_INTERVAL_MS) {
            ESP_LOGW("ble", "backlog drops stopped: %lu more since the last warning (%lu total)",
                     (unsigned long) nDroppedSinceWarn, (unsigned long) nDroppedBacklog);
            tLastBacklogWarn = now;
            nDroppedSinceWarn = 0;
        }
        if (nIndicateFailedSinceWarn && now - tLastIndicateWarn >= WARN_INTERVAL_MS) {
            ESP_LOGW("ble", "indicate failures stopped: %lu more since the last warning "
                     "(%lu total)", (unsigned long) nIndicateFailedSinceWarn,
                     (unsigned long) nIndicateFailed);
            tLastIndicateWarn = now;
            nIndicateFailedSinceWarn = 0;
        }
    }

    void flush() override {
        consumeSessionChange();
        drainWarnCounters();
        if (otaBleActive()) return; // see send()
        if (acked || ackFailed) {
            // Consume the ack here, in the app task, instead of inside onAck (host task):
            // only the bytes the acked indication covered leave the buffer, the tail that
            // send() queued since moves to the front and goes out with the next indication.
            // A failed indication retires without consuming -- the payload goes out again.
            const bool consume = acked;
            acked = false;
            ackFailed = false;
            waitingForAck = 0;
            if (consume) {
                if (inFlightLen > bleBufPos) {
                    // No path is known to produce this; if it ever fires the bookkeeping is
                    // wrong and silently clamping would hide it.
                    ESP_LOGE("ble", "inFlightLen %hu > bleBufPos %hu", inFlightLen, bleBufPos);
                    inFlightLen = bleBufPos;
                }
                memmove(bleBuf, bleBuf + inFlightLen, bleBufPos - inFlightLen);
                bleBufPos -= inFlightLen;
            }
            inFlightLen = 0;
            ackWarned = false;
        }
        if (inTransmission()) {
            /* AN UNACKED INDICATION IS WAITED OUT, NOT RE-SENT. This used to clear waitingForAck
             * and inFlightLen after ACK_TIMEOUT_MS and indicate again, on the theory that the
             * re-send replaced a lost payload. It does not: NimBLE's
             * ble_gatts_indicate_custom() (ble_gattc.c:4860) allocates a fresh ble_gattc_proc and
             * mbuf per call and QUEUES the new indication behind the outstanding ATT request --
             * it never replaces or rejects it. So an application-level retry cannot reach the
             * peer any sooner than the original will, and it costs a proc, an mbuf, and -- fatally
             * -- a second pending completion that this code cannot tell apart from the first.
             *
             * That ambiguity is the real defect. onStatus carries no identity, and `acked` is a
             * bool, so with two indications outstanding the FIRST completion retires the SECOND
             * one's inFlightLen. Since send() keeps appending, the second is usually longer, and
             * the difference is records retired from the queue that nothing ever confirmed. A
             * disconnect before the queued indication drains loses them silently -- the exact
             * class of invisible loss this whole file exists to prevent. Clamping the re-send's
             * length (the previous attempt at a fix) narrows the window but cannot close it,
             * because each further timeout adds another untracked completion.
             *
             * With no retry there is at most ONE indication outstanding at any time, which is
             * precisely what a bool can represent. The timeout keeps its value as a DIAGNOSTIC --
             * it says the link is slow -- and the buffer is unparked by ACK_STUCK_MS below rather
             * than by stacking payloads. */
            const uint32_t waited = millis() - tLastIndicate;
            if (waited >= ACK_STUCK_MS) {
                /* The escape hatch, and the reason "must not park the buffer forever" still
                 * holds. Per the ATT spec a transaction that never completes is fatal to the
                 * bearer, and NimBLE's own 30 s GATT timeout should have terminated the procedure
                 * well before this. If it has not, the host is wedged and only a fresh session
                 * recovers it -- onDisconnect sets sessionChanged, which discards the buffer and
                 * every scrap of transfer state. Losing the queue is the point: none of it can be
                 * accounted for any more. */
                ESP_LOGE("ble", "no ack for %ums -- ATT bearer is stuck, dropping the link",
                         (unsigned) waited);
                if (pServer) pServer->disconnect(connHandle);
                return;
            }
            if (waited >= ACK_TIMEOUT_MS && !ackWarned) {
                // Once per outstanding indication, not once per ACK_TIMEOUT_MS: flush() runs at
                // the app-task rate now, and this used to be the trigger for a re-send rather
                // than a log line, so it fired on a schedule. It is a slow-link report.
                ackWarned = true;
                ESP_LOGW("ble", "no ack for %ums, waiting (queue %hu bytes)",
                         (unsigned) waited, bleBufPos);
            }
            return;
        }
        if (!isConnected()) {
            return;
        }

        // NimBLE turned us away recently: give its mbuf pool a connection interval to refill
        // rather than retrying at the app-task rate. See tIndicateFailed.
        if (tIndicateFailed && millis() - tIndicateFailed < INDICATE_BACKOFF_MS) return;

        if (pCharacteristic && bleBufPos && subscribed) {
            /* One indication carries at most one ATT payload. bleBufLen is now
             * several payloads deep, so this MUST be clamped. The tail stays
             * queued and the ack path's memmove brings it forward for the next
             * indication.
             *
             * CLAMP TO THE NEGOTIATED MTU, NOT THE REQUESTED ONE. MAX_PAYLOAD_LEN
             * is MTU-3 = 509 for the 512 we ASK for, but the comment on peerMtu
             * says plainly that we do not always get it --
             * CONFIG_BT_NIMBLE_ATT_PREFERRED_MTU=256 in the prebuilt libs caps it.
             * NimBLE truncates an oversized indication to the negotiated MTU and
             * still returns success, so with peerMtu=256 only 253 of 509 bytes
             * would reach the central while the ack retired all 509: samples
             * silently lost, and the collector fed a half frame that fails CRC
             * and desynchronises its parser.
             *
             * This was latent before batching -- send() flushed eagerly, so
             * bleBufPos was usually one 64-byte sample and never approached the
             * cap. Filling the buffer is what made it reachable, which is why the
             * bound belongs here and not only in drainOtaTx() (ble.h:462), where
             * it was already being done correctly. */
            const uint16_t attPayload = peerMtu > 3 ? (uint16_t) (peerMtu - 3) : 20;
            uint16_t cap = attPayload < MAX_PAYLOAD_LEN ? attPayload : MAX_PAYLOAD_LEN;

            /* ROUND THE CAP DOWN TO A WHOLE RECORD -- see MAX_INDICATE_LEN. The
             * MTU clamp above is necessary but not sufficient: 253 and 509 are
             * both mid-record, and the no-ack path at the top of this function
             * re-sends the SAME byte range, so a late ack for an indication the
             * peer did receive injects a partial record into a byte stream the
             * collector frames by `len(d) % 64`. Every boundary after it is
             * wrong, permanently. Whole records instead duplicate cleanly, and
             * the resulting InfluxDB points carry the same tags and timestamp,
             * so they overwrite rather than double-count. */
            if (cap >= RECORD_LEN) {
                cap = (uint16_t) ((cap / RECORD_LEN) * RECORD_LEN);
            } else {
                /* An MTU too small for one 64-byte record. Ship the unaligned
                 * bytes anyway: the collector reassembles a split record
                 * correctly in the normal case, so best-effort delivery beats a
                 * permanent silent stall -- which is what returning here would
                 * be, since nothing would ever drain the buffer again. Loud,
                 * because telemetry on such a link is degraded by design and the
                 * resend hazard above is live. */
                static uint16_t lastWarnedMtu = 0;
                if (lastWarnedMtu != peerMtu) {
                    lastWarnedMtu = peerMtu;
                    ESP_LOGW("ble", "peer MTU %hu leaves %hu payload bytes, under one %hu-byte "
                                    "record -- indications cannot be record-aligned and a "
                                    "re-sent payload may desynchronise the collector",
                             peerMtu, attPayload, RECORD_LEN);
                }
            }
            const uint16_t sendLen = bleBufPos > cap ? cap : bleBufPos;
            /* DEBUG, not INFO: one line per indication is ~2/s forever and it
             * buried the sampler summaries. Nothing is lost by hiding it --
             * every case worth acting on has its own WARNING (indicate failed,
             * no-ack re-arm, buffer full with a subscriber attached), and drops
             * are counted in nDroppedBacklog rather than inferred from this.
             * Rebuild with -DCORE_DEBUG_LEVEL=4 to watch batching behaviour. */
            ESP_LOGD("ble", "sending %hu of %hu queued", sendLen, bleBufPos);
            //pCharacteristic->setValue(const_cast<uint8_t *>(buf), len);
            bool res = pCharacteristic->indicate(bleBuf, sendLen);
            if (!res) {
                // Throttled for the same reason as the backlog warning: flush() is now called at
                // the app-task rate, so a congested host would produce ~100 identical lines/s.
                ++nIndicateFailed;
                ++nIndicateFailedSinceWarn;
                tIndicateFailed = millis();
                if (!tLastIndicateWarn || tIndicateFailed - tLastIndicateWarn >= WARN_INTERVAL_MS) {
                    ESP_LOGW("ble", "indicate failed %lu time(s) since the last warning (%lu total)",
                             (unsigned long) nIndicateFailedSinceWarn,
                             (unsigned long) nIndicateFailed);
                    tLastIndicateWarn = tIndicateFailed;
                    nIndicateFailedSinceWarn = 0;
                }
            } else {
                tIndicateFailed = 0; // disarm the backoff; nIndicateFailed stays a running total
                inFlightLen = sendLen;
                ++waitingForAck;
                tLastIndicate = millis();
            }
        }
    }

    class ServerCallbacks : public NimBLEServerCallbacks {
        BleSrv *srv;

    public:
        explicit ServerCallbacks(BleSrv *srv) : srv{srv} {
        }

    private:
        void onConnect(NimBLEServer *pServer, NimBLEConnInfo &connInfo) override {
            Serial.printf("Client address: %s\n", connInfo.getAddress().toString().c_str());

            /**
             *  Connection parameters -- min/max interval in 1.25ms units, latency in intervals,
             *  supervision timeout in 10ms units -- are requested from the app task, not here.
             *  Issuing a device-initiated LL connection update synchronously from inside the connect
             *  callback trips a controller assert (lld_con.c:3275); BleSrv::tick() applies it a pass
             *  later, which is soon enough and cannot assert.
             */
            // Accept whatever the central negotiated; tick() requests nothing in steady state.
            srv->connHandle = connInfo.getConnHandle();
            srv->haveConn = true; // set last: it is what gates tick()
            srv->auxPublished = -1; // force tick() to re-publish for the new client
        }

        void onDisconnect(NimBLEServer *pServer, NimBLEConnInfo &connInfo, int reason) override {
            Serial.printf("Client disconnected (reason %d) - start advertising\n", reason);
            srv->onDisconnected();
            srv->haveConn = false;
            srv->peerMtu = 23;
            // Harmless when no transfer is in flight -- otaBleRequestAbort() ignores it -- which
            // matters, because this fires for every ordinary telemetry disconnect too.
            otaBleRequestAbort();
            // Unchecked, this is the difference between "the peer went away" and "this
            // device is never reachable again", with nothing in the log to tell them
            // apart. That is exactly the symptom we spent a day chasing from the client
            // side, so it says so if it fails.
            if (!NimBLEDevice::startAdvertising()) {
                ESP_LOGE("ble", "startAdvertising() FAILED after disconnect -- unreachable");
            }
        }

        void onMTUChange(uint16_t MTU, NimBLEConnInfo &connInfo) override {
            Serial.printf("MTU updated: %u for connection ID: %u\n", MTU, connInfo.getConnHandle());
            srv->peerMtu = MTU; // notifications are chunked to this, so it has to be kept, not just printed
        }

        /********************* Security handled here *********************/
        uint32_t onPassKeyDisplay() override {
            Serial.printf("Server Passkey Display\n");
            /**
             * This should return a random 6 digit number for security
             *  or make your own static passkey as done here.
             */
            return 123456;
        }

        void onConfirmPassKey(NimBLEConnInfo &connInfo, uint32_t pass_key) override {
            Serial.printf("The passkey YES/NO number: %" PRIu32 "\n", pass_key);
            /** Inject false if passkeys don't match. */
            NimBLEDevice::injectConfirmPasskey(connInfo, true);
        }

        void onAuthenticationComplete(NimBLEConnInfo &connInfo) override {
            /** Check that encryption was successful, if not we disconnect the client */
            if (!connInfo.isEncrypted()) {
                NimBLEDevice::getServer()->disconnect(connInfo.getConnHandle());
                Serial.printf("Encrypt connection failed - disconnecting client\n");
                return;
            }

            Serial.printf("Secured connection to: %s\n", connInfo.getAddress().toString().c_str());
        }
    } serverCallbacks;

    void onAck(bool done) {
        if (waitingForAck) {
            // Host-task context: report only. flush() clears waitingForAck and consumes the
            // buffer in the app task.
            if (done) acked = true;
            else ackFailed = true;
        } else {
            // A status callback with nothing in flight is reachable: a session change zeroes
            // the counter while an indication is still outstanding, and the abandoned
            // indication reports later. Attributing it to anything would consume bytes it
            // never covered, so it is only logged.
            ESP_LOGW("ble", "onAck (done=%i) with no indication in flight, ignored", (int) done);
        }
        /* DEBUG for the same reason as flush()'s send line: this fires once per
         * indication, pairing with it at ~2/s. A FAILED ack is the interesting
         * case and it is handled below on its own path, not inferred from here. */
        ESP_LOGD("ble", "onAck done=%i waiting=%hhu", (int)done, waitingForAck);
    }

    void onCharSub(bool sub) {
        // Host-task context: flags only, see the single-writer rule at the top.
        subscribed = sub;
        sessionChanged = true;
        if (sub && nDroppedNoPeer) {
            ESP_LOGI("ble", "subscriber attached, %lu samples were discarded unsent",
                     (unsigned long) nDroppedNoPeer);
            nDroppedNoPeer = 0;
        }
    }

    /** Handler class for characteristic actions */
    class CharacteristicCallbacks : public NimBLECharacteristicCallbacks {
        BleSrv *srv;

    public:
        explicit CharacteristicCallbacks(BleSrv *srv) : srv{srv} {
        }

        void onRead(NimBLECharacteristic *pCharacteristic, NimBLEConnInfo &connInfo) override {
            Serial.printf("%s : onRead(), value: %s\n",
                          pCharacteristic->getUUID().toString().c_str(),
                          pCharacteristic->getValue().c_str());
        }

        void onWrite(NimBLECharacteristic *pCharacteristic, NimBLEConnInfo &connInfo) override {
            Serial.printf("%s : onWrite(), value: %s\n",
                          pCharacteristic->getUUID().toString().c_str(),
                          pCharacteristic->getValue().c_str());
        }

        /**
         *  The value returned in code is the NimBLE host return code.
         */
        void onStatus(NimBLECharacteristic *pCharacteristic, int code) override {
            srv->onAck(code == BLE_HS_EDONE);
            if (code != BLE_HS_EDONE) {
                Serial.printf("Notification/Indication return code: %d, %s\n", code,
                              NimBLEUtils::returnCodeToString(code));
            }
        }

        /** Peer subscribed to notifications/indications */
        void onSubscribe(NimBLECharacteristic *pCharacteristic, NimBLEConnInfo &connInfo, uint16_t subValue) override {
            std::string str = "Client ID: ";
            str += connInfo.getConnHandle();
            str += " Address: ";
            str += connInfo.getAddress().toString();
            if (subValue == 0) {
                str += " Unsubscribed to ";
                srv->onCharSub(false);
            } else if (subValue == 1) {
                str += " Subscribed to notifications for ";
            } else if (subValue == 2) {
                str += " Subscribed to indications for ";
                srv->onCharSub(true);
            } else if (subValue == 3) {
                str += " Subscribed to notifications and indications for ";
            }
            str += std::string(pCharacteristic->getUUID());

            Serial.printf("%s\n", str.c_str());
        }
    } chrCallbacks;

    /// OTA control plane. Runs on the NimBLE host task, so it only parses and latches -- otaBleTick()
    /// on the app task does the flash work, which blocks for far longer than a host callback may.
    class OtaCtrlCallbacks : public NimBLECharacteristicCallbacks {
        BleSrv *srv;

    public:
        explicit OtaCtrlCallbacks(BleSrv *srv) : srv{srv} {
        }

        void onWrite(NimBLECharacteristic *pCharacteristic, NimBLEConnInfo &connInfo) override {
            std::string v = pCharacteristic->getValue();
            // Tolerate a client that sends the newline the protocol is written with.
            while (!v.empty() && (v.back() == '\n' || v.back() == '\r')) v.pop_back();
            if (v.empty()) return;
            /* Reboot into the ROM downloader. Lives on the OTA control channel
             * because that is where "I am about to reflash this" belongs, and
             * because adding a characteristic would change the GATT table --
             * which doc/ota-over-ble.md warns makes macOS serve a stale cached
             * attribute table to every client until it is manually busted.
             *
             * Latch only. This is the NimBLE host task; the app task does the
             * reboot so the confirming notification can actually go out first. */
            if (v == "download") {
                srv->dlReqPending = true;
                return;
            }
            // A rejection is announced by the module itself, on the same OTAB status channel as
            // every other failure -- nothing to add here beyond echoing what was actually sent.
            if (otaBleSubmitCommand(v.c_str()) == OtaBleSubmit::Rejected)
                ESP_LOGW("otab", "rejected command: %s", v.c_str());
        }
    } otaCtrlCallbacks;

    /// Aux switch control. Host-task context: parse and latch only -- applying it writes NVS.
    class AuxCallbacks : public NimBLECharacteristicCallbacks {
        BleSrv *srv;

    public:
        explicit AuxCallbacks(BleSrv *srv) : srv{srv} {
        }

        void onWrite(NimBLECharacteristic *pCharacteristic, NimBLEConnInfo &connInfo) override {
            std::string v = pCharacteristic->getValue();
            bool want;
            if (!auxParseCommand((const uint8_t *) v.data(), v.size(), want)) {
                ESP_LOGW("aux", "unparseable aux write (%u bytes), ignored", (unsigned) v.size());
                // Re-publish so the characteristic value never reflects the garbage that was
                // written into it, and the client can see the switch did not move.
                srv->publishAux(auxGet());
                return;
            }
            srv->auxReqValue = want;
            srv->auxReqPending = true;
        }
    } auxCallbacks;

    /// OTA data plane: copy into the staging ring and return. Nothing here may touch flash.
    class OtaDataCallbacks : public NimBLECharacteristicCallbacks {
    public:
        void onWrite(NimBLECharacteristic *pCharacteristic, NimBLEConnInfo &connInfo) override {
            std::string v = pCharacteristic->getValue();
            otaBleStageBytes((const uint8_t *) v.data(), v.size());
        }
    } otaDataCallbacks;
};


#endif
