open-pe/smart-shunt-fw/src/aux_switch.h

#pragma once

#include <Arduino.h>
#include <EEPROM.h>

#ifdef TARGET_STM32H5
#include "esp_compat.h"
constexpr uint8_t AUX_PIN = PA8;
#else
#include <driver/gpio.h>
#include <esp_log.h>

/*
 * Aux switch: one general-purpose GPIO output, driven from BLE or the console.
 *
 * GPIO 9 is free (undeclared in settings.h), not a strapping pin, not USB, not flash, and is
 * RTC-capable -- that last part is what lets it hold its level through deep sleep. Confirm the pin
 * is actually broken out on the module before wiring: hw/ documents the INA228 sensor board (whose
 * MCU sheet is an ESP-12F), not the ESP32-S3 module the firmware runs on.
 *
 * The pin FLOATS from reset until auxBegin() runs. Nothing in firmware can cover that window, so the
 * N-channel MOSFET gate needs an external pulldown to keep the load off through boot.
 */

constexpr gpio_num_t AUX_PIN = GPIO_NUM_9;
#endif
/* Load-switch gate polarity is board-specific. The default (1) is the N-channel low-side
 * switch the bench boards are wired for: HIGH = on, LOW = off. A board still on the old
 * P-channel high-side switch MUST be built with -D AUX_ACTIVE_HIGH=0 -- otherwise a logical
 * "off" drives the gate LOW and physically energises the load at boot, and "aux off" makes
 * it more on. There is no runtime detection; polarity is a compile-time per-board fact. */
#ifndef AUX_ACTIVE_HIGH
#  define AUX_ACTIVE_HIGH 1
#endif

/* Not every board carries the load switch. A bring-up rig that has none must not merely
 * leave it "off" -- it must not drive AUX_PIN AT ALL, because on such a board that pad is
 * usually doing something else. Concretely: on the XIAO ESP32-S3 carrying the pwr-metering
 * shunt-adc board, GPIO9 is J2.3 / SCLK, and auxBegin()'s pinMode(OUTPUT) plus
 * auxArmDeepSleepHold()'s gpio_hold_en() would put a held output pad in contention with the
 * SPI peripheral's clock line. Build those with -D AUX_PIN_PRESENT=0.
 *
 * This suppresses the PIN, not the state machine: the console and BLE surfaces stay
 * compiled, and both echo auxGet() after every set, so a refused request reads back "off"
 * at the caller instead of being silently accepted. The persisted state is also ignored --
 * an EEPROM image carried over from a board that DID have the switch would otherwise come
 * back "ON", pin idle sleep open through stayAwake, and publish a switch that isn't there. */
#ifndef AUX_PIN_PRESENT
#  define AUX_PIN_PRESENT 1
#endif

// Raw EEPROM/NVS byte offsets -- deliberately NOT slot indices. Calibration occupies bytes 16..111
// today and its assert(ecIndex <= 16) reserves through 151, and the slot scheme is already
// over-subscribed (slot 4 is shared by INA226 range and INA228@0x42, slot 8 by TMP117@0x4B and an
// INA228 range), so allocating another index would be asking for a third collision.
constexpr int AUX_NVS_MAGIC_ADDR = 152;
constexpr int AUX_NVS_STATE_ADDR = 153;
constexpr uint8_t AUX_NVS_MAGIC = 0x5A;
constexpr size_t AUX_NVS_SIZE = 256; // same image size every other EEPROM user opens

static bool auxState = false;

inline bool auxGet() { return auxState; }

/// Read the persisted state without trusting an unwritten blob. A virgin NVS image reads back as
/// zeros, so without the magic byte "never written" and "written off" are indistinguishable -- and
/// any encoding where the *absence* of a record could mean "on" would energise a load on a blank
/// device. Off is the only safe reading of "I don't know".
inline bool auxReadPersisted() {
#ifdef TARGET_STM32H5
    uint8_t magic = EEPROM.read(AUX_NVS_MAGIC_ADDR);
    uint8_t st = EEPROM.read(AUX_NVS_STATE_ADDR);
    if (magic != AUX_NVS_MAGIC) return false;
    return st == 1;
#else
    EEPROM.begin(AUX_NVS_SIZE);
    uint8_t magic = EEPROM.read(AUX_NVS_MAGIC_ADDR);
    uint8_t st = EEPROM.read(AUX_NVS_STATE_ADDR);
    EEPROM.end();
    if (magic != AUX_NVS_MAGIC) return false;
    return st == 1;
#endif
}

inline void auxWritePersisted(bool on) {
#ifdef TARGET_STM32H5
    EEPROM.write(AUX_NVS_MAGIC_ADDR, AUX_NVS_MAGIC);
    EEPROM.write(AUX_NVS_STATE_ADDR, on ? 1 : 0);
#else
    EEPROM.begin(AUX_NVS_SIZE);
    EEPROM.write(AUX_NVS_MAGIC_ADDR, AUX_NVS_MAGIC);
    EEPROM.write(AUX_NVS_STATE_ADDR, on ? 1 : 0);
    EEPROM.commit();
    EEPROM.end();
#endif
}

inline void auxDrive(bool on) {
#if AUX_PIN_PRESENT
    digitalWrite(AUX_PIN, (on == AUX_ACTIVE_HIGH) ? HIGH : LOW);
#else
    (void) on;   // no switch fitted -- AUX_PIN belongs to something else on this board
#endif
}

/// Call early in setup(), before the long init work -- on a deep-sleep wake the load has been
/// carried across by the pad hold and should be handed back to the firmware promptly.
inline void auxBegin() {
#if !AUX_PIN_PRESENT
    // Do not read the persisted state either: see AUX_PIN_PRESENT above.
    auxState = false;
    ESP_LOGI("aux", "no aux switch on this board (AUX_PIN_PRESENT=0); GPIO%d left alone",
             (int) AUX_PIN);
    return;
#else
    auxState = auxReadPersisted();

    // Order matters coming out of deep sleep, where the pad is still held at its old level:
    // configure the peripheral FIRST, while the hold masks it, then release. Releasing first would
    // let the pad follow its reset default for the microseconds until digitalWrite lands -- a blink
    // of the load on every wake.
    pinMode(AUX_PIN, OUTPUT);
    auxDrive(auxState);
#ifdef TARGET_STM32H5
    // No deep-sleep pad hold on STM32H5 (Stop mode not implemented yet)
#else
    gpio_hold_dis(AUX_PIN);
#endif

    ESP_LOGI("aux", "aux switch on GPIO%d = %s (restored)", (int) AUX_PIN, auxState ? "ON" : "off");
#endif
}

/// App-task only. Persists only on an actual change: EEPROM.commit() rewrites the whole 256-byte
/// blob, and re-asserting a value that is already stored would burn a flash cycle for nothing.
inline void auxSet(bool on) {
#if !AUX_PIN_PRESENT
    // Refuse rather than record. Both callers re-read auxGet() and report it, so the
    // request visibly fails instead of leaving a phantom "ON" the board cannot honour.
    if (on) ESP_LOGW("aux", "no aux switch on this board; request ignored");
    return;
#endif
    if (on == auxState) return;
    auxState = on;
    auxDrive(on);
    auxWritePersisted(on);
    ESP_LOGI("aux", "aux switch -> %s", on ? "ON" : "off");
}

/// Latch the pad so the level survives deep sleep and the wake reset. Without this the switch would
/// drop out for the whole boot interval every time the idle sleep cycles -- every 15 minutes.
inline void auxArmDeepSleepHold() {
#if !AUX_PIN_PRESENT
    return;   // holding a pad that belongs to SPI is exactly what this knob exists to prevent
#elif defined(TARGET_STM32H5)
    // No deep-sleep pad hold on STM32H5 yet
#else
    gpio_hold_en(AUX_PIN);
    gpio_deep_sleep_hold_en();
#endif
}

/// Parse a command payload. Accepts the ASCII digits and raw bytes a generic BLE app would send as
/// well as words, so the switch is usable from something other than our own tooling.
/// Returns false if nothing recognisable was found; `out` is only written on success.
inline bool auxParseCommand(const uint8_t *data, size_t len, bool &out) {
    if (!data || !len) return false;
    if (len == 1 && (data[0] == 0 || data[0] == 1)) { out = data[0] != 0; return true; }

    String s;
    for (size_t i = 0; i < len; ++i) s += (char) data[i];
    s.trim();
    s.toLowerCase();

    if (s == "1" || s == "on" || s == "true") { out = true; return true; }
    if (s == "0" || s == "off" || s == "false") { out = false; return true; }
    if (s == "toggle") { out = !auxGet(); return true; }
    return false;
}
