open-pe/smart-shunt-fw/src/readerwriterqueue.h

// ©2013-2020 Cameron Desrochers.
// Distributed under the simplified BSD license (see the license file that
// should have come with this header).

#pragma once

#include "atomicops.h"
#include <new>
#include <type_traits>
#include <utility>
#include <cassert>
#include <stdexcept>
#include <new>
#include <cstdint>
#include <cstdlib>		// For malloc/free/abort & size_t
#include <memory>
#if __cplusplus > 199711L || _MSC_VER >= 1700 // C++11 or VS2012
#include <chrono>
#endif


// A lock-free queue for a single-consumer, single-producer architecture.
// The queue is also wait-free in the common path (except if more memory
// needs to be allocated, in which case malloc is called).
// Allocates memory sparingly, and only once if the original maximum size
// estimate is never exceeded.
// Tested on x86/x64 processors, but semantics should be correct for all
// architectures (given the right implementations in atomicops.h), provided
// that aligned integer and pointer accesses are naturally atomic.
// Note that there should only be one consumer thread and producer thread;
// Switching roles of the threads, or using multiple consecutive threads for
// one role, is not safe unless properly synchronized.
// Using the queue exclusively from one thread is fine, though a bit silly.

#ifndef MOODYCAMEL_CACHE_LINE_SIZE
#define MOODYCAMEL_CACHE_LINE_SIZE 64
#endif

#ifndef MOODYCAMEL_EXCEPTIONS_ENABLED
#if (defined(_MSC_VER) && defined(_CPPUNWIND)) || (defined(__GNUC__) && defined(__EXCEPTIONS)) || (!defined(_MSC_VER) && !defined(__GNUC__))
#define MOODYCAMEL_EXCEPTIONS_ENABLED
#endif
#endif

#ifndef MOODYCAMEL_HAS_EMPLACE
#if !defined(_MSC_VER) || _MSC_VER >= 1800 // variadic templates: either a non-MS compiler or VS >= 2013
#define MOODYCAMEL_HAS_EMPLACE    1
#endif
#endif

#ifndef MOODYCAMEL_MAYBE_ALIGN_TO_CACHELINE
#if defined (__APPLE__) && defined (__MACH__) && __cplusplus >= 201703L
// This is required to find out what deployment target we are using
#include <AvailabilityMacros.h>
#if !defined(MAC_OS_X_VERSION_MIN_REQUIRED) || !defined(MAC_OS_X_VERSION_10_14) || MAC_OS_X_VERSION_MIN_REQUIRED < MAC_OS_X_VERSION_10_14
// C++17 new(size_t, align_val_t) is not backwards-compatible with older versions of macOS, so we can't support over-alignment in this case
#define MOODYCAMEL_MAYBE_ALIGN_TO_CACHELINE
#endif
#endif
#endif

#ifndef MOODYCAMEL_MAYBE_ALIGN_TO_CACHELINE
#define MOODYCAMEL_MAYBE_ALIGN_TO_CACHELINE AE_ALIGN(MOODYCAMEL_CACHE_LINE_SIZE)
#endif

#ifdef AE_VCPP
#pragma warning(push)
#pragma warning(disable: 4324)	// structure was padded due to __declspec(align())
#pragma warning(disable: 4820)	// padding was added
#pragma warning(disable: 4127)	// conditional expression is constant
#endif

namespace moodycamel {

    template<typename T, size_t MAX_BLOCK_SIZE = 512>
    class MOODYCAMEL_MAYBE_ALIGN_TO_CACHELINE ReaderWriterQueue
{
    // Design: Based on a queue-of-queues. The low-level queues are just
    // circular buffers with front and tail indices indicating where the
    // next element to dequeue is and where the next element can be enqueued,
    // respectively. Each low-level queue is called a "block". Each block
    // wastes exactly one element's worth of space to keep the design simple
    // (if front == tail then the queue is empty, and can't be full).
    // The high-level queue is a circular linked list of blocks; again there
    // is a front and tail, but this time they are pointers to the blocks.
    // The front block is where the next element to be dequeued is, provided
    // the block is not empty. The back block is where elements are to be
    // enqueued, provided the block is not full.
    // The producer thread owns all the tail indices/pointers. The consumer
    // thread owns all the front indices/pointers. Both threads read each
    // other's variables, but only the owning thread updates them. E.g. After
    // the consumer reads the producer's tail, the tail may change before the
    // consumer is done dequeuing an object, but the consumer knows the tail
    // will never go backwards, only forwards.
    // If there is no room to enqueue an object, an additional block (of
    // equal size to the last block) is added. Blocks are never removed.

    public:
    typedef T value_type;

    // Constructs a queue that can hold at least `size` elements without further
    // allocations. If more than MAX_BLOCK_SIZE elements are requested,
    // then several blocks of MAX_BLOCK_SIZE each are reserved (including
    // at least one extra buffer block).
    AE_NO_TSAN explicit ReaderWriterQueue(size_t size = 15)
#ifndef NDEBUG
    : enqueuing(false)
    ,dequeuing(false)
#endif
{
    assert(MAX_BLOCK_SIZE == ceilToPow2(MAX_BLOCK_SIZE) && "MAX_BLOCK_SIZE must be a power of 2");
    assert(MAX_BLOCK_SIZE >= 2 && "MAX_BLOCK_SIZE must be at least 2");

    Block* firstBlock = nullptr;

    largestBlockSize = ceilToPow2(size + 1);		// We need a spare slot to fit size elements in the block
    if (largestBlockSize > MAX_BLOCK_SIZE * 2) {
    // We need a spare block in case the producer is writing to a different block the consumer is reading from, and
    // wants to enqueue the maximum number of elements. We also need a spare element in each block to avoid the ambiguity
    // between front == tail meaning "empty" and "full".
    // So the effective number of slots that are guaranteed to be usable at any time is the block size - 1 times the
    // number of blocks - 1. Solving for size and applying a ceiling to the division gives us (after simplifying):
    size_t initialBlockCount = (size + MAX_BLOCK_SIZE * 2 - 3) / (MAX_BLOCK_SIZE - 1);
    largestBlockSize = MAX_BLOCK_SIZE;
    Block* lastBlock = nullptr;
    for (size_t i = 0; i != initialBlockCount; ++i) {
    auto block = make_block(largestBlockSize);
    if (block == nullptr) {
#ifdef MOODYCAMEL_EXCEPTIONS_ENABLED
    throw std::bad_alloc();
#else
    abort();
#endif
}
if (firstBlock == nullptr) {
firstBlock = block;
}
else {
lastBlock->next = block;
}
lastBlock = block;
block->next = firstBlock;
}
}
else {
firstBlock = make_block(largestBlockSize);
if (firstBlock == nullptr) {
#ifdef MOODYCAMEL_EXCEPTIONS_ENABLED
throw std::bad_alloc();
#else
abort();
#endif
}
firstBlock->next = firstBlock;
}
frontBlock = firstBlock;
tailBlock = firstBlock;

// Make sure the reader/writer threads will have the initialized memory setup above:
fence(memory_order_sync);
}

// Note: The queue should not be accessed concurrently while it's
// being moved. It's up to the user to synchronize this.
AE_NO_TSAN ReaderWriterQueue(ReaderWriterQueue&& other)
: frontBlock(other.frontBlock.load()),
tailBlock(other.tailBlock.load()),
largestBlockSize(other.largestBlockSize)
#ifndef NDEBUG
,enqueuing(false)
,dequeuing(false)
#endif
{
other.largestBlockSize = 32;
Block* b = other.make_block(other.largestBlockSize);
if (b == nullptr) {
#ifdef MOODYCAMEL_EXCEPTIONS_ENABLED
throw std::bad_alloc();
#else
abort();
#endif
}
b->next = b;
other.frontBlock = b;
other.tailBlock = b;
}

// Note: The queue should not be accessed concurrently while it's
// being moved. It's up to the user to synchronize this.
ReaderWriterQueue& operator=(ReaderWriterQueue&& other) AE_NO_TSAN
{
Block* b = frontBlock.load();
frontBlock = other.frontBlock.load();
other.frontBlock = b;
b = tailBlock.load();
tailBlock = other.tailBlock.load();
other.tailBlock = b;
std::swap(largestBlockSize, other.largestBlockSize);
return *this;
}

// Note: The queue should not be accessed concurrently while it's
// being deleted. It's up to the user to synchronize this.
AE_NO_TSAN ~ReaderWriterQueue()
{
    // Make sure we get the latest version of all variables from other CPUs:
    fence(memory_order_sync);

    // Destroy any remaining objects in queue and free memory
    Block* frontBlock_ = frontBlock;
    Block* block = frontBlock_;
    do {
        Block* nextBlock = block->next;
        size_t blockFront = block->front;
        size_t blockTail = block->tail;

        for (size_t i = blockFront; i != blockTail; i = (i + 1) & block->sizeMask) {
            auto element = reinterpret_cast<T*>(block->data + i * sizeof(T));
            element->~T();
            (void)element;
        }

        auto rawBlock = block->rawThis;
        block->~Block();
        std::free(rawBlock);
        block = nextBlock;
    } while (block != frontBlock_);
}


// Enqueues a copy of element if there is room in the queue.
// Returns true if the element was enqueued, false otherwise.
// Does not allocate memory.
AE_FORCEINLINE bool try_enqueue(T const& element) AE_NO_TSAN
{
return inner_enqueue<CannotAlloc>(element);
}

// Enqueues a moved copy of element if there is room in the queue.
// Returns true if the element was enqueued, false otherwise.
// Does not allocate memory.
AE_FORCEINLINE bool try_enqueue(T&& element) AE_NO_TSAN
{
return inner_enqueue<CannotAlloc>(std::forward<T>(element));
}

#if MOODYCAMEL_HAS_EMPLACE
// Like try_enqueue() but with emplace semantics (i.e. construct-in-place).
template<typename... Args>
AE_FORCEINLINE bool try_emplace(Args&&... args) AE_NO_TSAN
{
return inner_enqueue<CannotAlloc>(std::forward<Args>(args)...);
}
#endif

// Enqueues a copy of element on the queue.
// Allocates an additional block of memory if needed.
// Only fails (returns false) if memory allocation fails.
AE_FORCEINLINE bool enqueue(T const& element) AE_NO_TSAN
{
return inner_enqueue<CanAlloc>(element);
}

// Enqueues a moved copy of element on the queue.
// Allocates an additional block of memory if needed.
// Only fails (returns false) if memory allocation fails.
AE_FORCEINLINE bool enqueue(T&& element) AE_NO_TSAN
{
return inner_enqueue<CanAlloc>(std::forward<T>(element));
}
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
